mecparts/TeensyBoardZ80/src/cpu.h

#ifndef CPU_H
#define CPU_H

/* see main.c for definition */

int32 PCX; /* external view of PC                          */
int32 AF;  /* AF register                                  */
int32 BC;  /* BC register                                  */
int32 DE;  /* DE register                                  */
int32 HL;  /* HL register                                  */
int32 IX;  /* IX register                                  */
int32 IY;  /* IY register                                  */
int32 PC;  /* program counter                              */
int32 SP;  /* SP register                                  */
int32 AF1; /* alternate AF register                        */
int32 BC1; /* alternate BC register                        */
int32 DE1; /* alternate DE register                        */
int32 HL1; /* alternate HL register                        */
int32 IFF; /* Interrupt Flip Flop                          */
int32 IR;  /* Interrupt (upper) / Refresh (lower) register */
enum StatusType { 
	RUNNING,
	CBOOT,
	WBOOT,
	RETCCP 
} Status = RUNNING; /* Status of the CPU 0=running 1=end request 2=back to CCP */
int32 Debug = 0;
int32 Break = -1;
int32 Step = -1;

#ifdef iDEBUG
FILE* iLogFile;
char iLogBuffer[16];
const char* iLogTxt;
#endif

/*
	Functions needed by the soft CPU implementation
*/
void cpu_out(const uint32 Port, const uint32 Value) {
	_Bios();
}

uint32 cpu_in(const uint32 Port) {
	_Bdos();
	return(HIGH_REGISTER(AF));
}

/* Z80 Custom soft core */

/* simulator stop codes */
#define STOP_HALT       0   /* HALT                                             */
#define STOP_IBKPT      1   /* breakpoint   (program counter)                   */
#define STOP_MEM        2   /* breakpoint   (memory access)                     */
#define STOP_INSTR      3   /* breakpoint   (instruction access)                */
#define STOP_OPCODE     4   /* invalid operation encountered (8080, Z80, 8086)  */

#define ADDRMASK        0xffff

#define FLAG_C  1
#define FLAG_N  2
#define FLAG_P  4
#define FLAG_H  16
#define FLAG_Z  64
#define FLAG_S  128

#define SETFLAG(f,c)    (AF = (c) ? AF | FLAG_ ## f : AF & ~FLAG_ ## f)
#define TSTFLAG(f)      ((AF & FLAG_ ## f) != 0)

#define PARITY(x)   parityTable[(x) & 0xff]

#define SET_PVS(s)  (((cbits >> 6) ^ (cbits >> 5)) & 4)
#define SET_PV      (SET_PVS(sum))
#define SET_PV2(x)  ((temp == (x)) << 2)

#define POP(x)  {                               \
    register uint32 y = RAM_PP(SP);             \
    x = y + (RAM_PP(SP) << 8);                  \
}

#define JPC(cond) {                             \
    if (cond) {                                 \
        PC = GET_WORD(PC);                      \
    } else {                                    \
        PC += 2;                                \
    }                                           \
}

#define CALLC(cond) {                           \
    if (cond) {                                 \
        register uint32 adrr = GET_WORD(PC);    \
        PUSH(PC + 2);                           \
        PC = adrr;                              \
    } else {                                    \
        PC += 2;                                \
    }                                           \
}

/* the following tables precompute some common subexpressions
parityTable[i]          0..255  (number of 1's in i is odd) ? 0 : 4
incTable[i]             0..256! (i & 0xa8) | (((i & 0xff) == 0) << 6) | (((i & 0xf) == 0) << 4)
decTable[i]             0..255  (i & 0xa8) | (((i & 0xff) == 0) << 6) | (((i & 0xf) == 0xf) << 4) | 2
cbitsTable[i]           0..511  (i & 0x10) | ((i >> 8) & 1)
cbitsDup8Table[i]       0..511  (i & 0x10) | ((i >> 8) & 1) | ((i & 0xff) << 8) | (i & 0xa8) | (((i & 0xff) == 0) << 6)
cbitsDup16Table[i]      0..511  (i & 0x10) | ((i >> 8) & 1) | (i & 0x28)
cbits2Table[i]          0..511  (i & 0x10) | ((i >> 8) & 1) | 2
rrcaTable[i]            0..255  ((i & 1) << 15) | ((i >> 1) << 8) | ((i >> 1) & 0x28) | (i & 1)
rraTable[i]             0..255  ((i >> 1) << 8) | ((i >> 1) & 0x28) | (i & 1)
addTable[i]             0..511  ((i & 0xff) << 8) | (i & 0xa8) | (((i & 0xff) == 0) << 6)
subTable[i]             0..255  ((i & 0xff) << 8) | (i & 0xa8) | (((i & 0xff) == 0) << 6) | 2
andTable[i]             0..255  (i << 8) | (i & 0xa8) | ((i == 0) << 6) | 0x10 | parityTable[i]
xororTable[i]           0..255  (i << 8) | (i & 0xa8) | ((i == 0) << 6) | parityTable[i]
rotateShiftTable[i]     0..255  (i & 0xa8) | (((i & 0xff) == 0) << 6) | parityTable[i & 0xff]
incZ80Table[i]          0..256! (i & 0xa8) | (((i & 0xff) == 0) << 6) | (((i & 0xf) == 0) << 4) | ((i == 0x80) << 2)
decZ80Table[i]          0..255  (i & 0xa8) | (((i & 0xff) == 0) << 6) | (((i & 0xf) == 0xf) << 4) | ((i == 0x7f) << 2) | 2
cbitsZ80Table[i]        0..511  (i & 0x10) | (((i >> 6) ^ (i >> 5)) & 4) | ((i >> 8) & 1)
cbitsZ80DupTable[i]     0..511  (i & 0x10) | (((i >> 6) ^ (i >> 5)) & 4) | ((i >> 8) & 1) | (i & 0xa8)
cbits2Z80Table[i]       0..511  (i & 0x10) | (((i >> 6) ^ (i >> 5)) & 4) | ((i >> 8) & 1) | 2
cbits2Z80DupTable[i]    0..511  (i & 0x10) | (((i >> 6) ^ (i >> 5)) & 4) | ((i >> 8) & 1) | 2 | (i & 0xa8)
negTable[i]             0..255  (((i & 0x0f) != 0) << 4) | ((i == 0x80) << 2) | 2 | (i != 0)
rrdrldTable[i]          0..255  (i << 8) | (i & 0xa8) | (((i & 0xff) == 0) << 6) | parityTable[i]
cpTable[i]              0..255  (i & 0x80) | (((i & 0xff) == 0) << 6)
*/

/* parityTable[i] = (number of 1's in i is odd) ? 0 : 4, i = 0..255 */
static const uint8 parityTable[256] = {
	4,0,0,4,0,4,4,0,0,4,4,0,4,0,0,4,
	0,4,4,0,4,0,0,4,4,0,0,4,0,4,4,0,
	0,4,4,0,4,0,0,4,4,0,0,4,0,4,4,0,
	4,0,0,4,0,4,4,0,0,4,4,0,4,0,0,4,
	0,4,4,0,4,0,0,4,4,0,0,4,0,4,4,0,
	4,0,0,4,0,4,4,0,0,4,4,0,4,0,0,4,
	4,0,0,4,0,4,4,0,0,4,4,0,4,0,0,4,
	0,4,4,0,4,0,0,4,4,0,0,4,0,4,4,0,
	0,4,4,0,4,0,0,4,4,0,0,4,0,4,4,0,
	4,0,0,4,0,4,4,0,0,4,4,0,4,0,0,4,
	4,0,0,4,0,4,4,0,0,4,4,0,4,0,0,4,
	0,4,4,0,4,0,0,4,4,0,0,4,0,4,4,0,
	4,0,0,4,0,4,4,0,0,4,4,0,4,0,0,4,
	0,4,4,0,4,0,0,4,4,0,0,4,0,4,4,0,
	0,4,4,0,4,0,0,4,4,0,0,4,0,4,4,0,
	4,0,0,4,0,4,4,0,0,4,4,0,4,0,0,4,
};

/* incTable[i] = (i & 0xa8) | (((i & 0xff) == 0) << 6) | (((i & 0xf) == 0) << 4), i = 0..256 */
static const uint8 incTable[257] = {
	80,  0,  0,  0,  0,  0,  0,  0,  8,  8,  8,  8,  8,  8,  8,  8,
	16,  0,  0,  0,  0,  0,  0,  0,  8,  8,  8,  8,  8,  8,  8,  8,
	48, 32, 32, 32, 32, 32, 32, 32, 40, 40, 40, 40, 40, 40, 40, 40,
	48, 32, 32, 32, 32, 32, 32, 32, 40, 40, 40, 40, 40, 40, 40, 40,
	16,  0,  0,  0,  0,  0,  0,  0,  8,  8,  8,  8,  8,  8,  8,  8,
	16,  0,  0,  0,  0,  0,  0,  0,  8,  8,  8,  8,  8,  8,  8,  8,
	48, 32, 32, 32, 32, 32, 32, 32, 40, 40, 40, 40, 40, 40, 40, 40,
	48, 32, 32, 32, 32, 32, 32, 32, 40, 40, 40, 40, 40, 40, 40, 40,
	144,128,128,128,128,128,128,128,136,136,136,136,136,136,136,136,
	144,128,128,128,128,128,128,128,136,136,136,136,136,136,136,136,
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
	0xd88c,0xd988,0xda88,0xdb8c,0xdc88,0xdd8c,0xde8c,0xdf88,
	0xe0a0,0xe1a4,0xe2a4,0xe3a0,0xe4a4,0xe5a0,0xe6a0,0xe7a4,
	0xe8ac,0xe9a8,0xeaa8,0xebac,0xeca8,0xedac,0xeeac,0xefa8,
	0xf0a4,0xf1a0,0xf2a0,0xf3a4,0xf4a0,0xf5a4,0xf6a4,0xf7a0,
	0xf8a8,0xf9ac,0xfaac,0xfba8,0xfcac,0xfda8,0xfea8,0xffac,
};

/* cpTable[i] = (i & 0x80) | (((i & 0xff) == 0) << 6), i = 0..255 */
static const uint8 cpTable[256] = {
	64,  0,  0,  0,  0,  0,  0,  0,  0,  0,  0,  0,  0,  0,  0,  0,
	0,  0,  0,  0,  0,  0,  0,  0,  0,  0,  0,  0,  0,  0,  0,  0,
	0,  0,  0,  0,  0,  0,  0,  0,  0,  0,  0,  0,  0,  0,  0,  0,
	0,  0,  0,  0,  0,  0,  0,  0,  0,  0,  0,  0,  0,  0,  0,  0,
	0,  0,  0,  0,  0,  0,  0,  0,  0,  0,  0,  0,  0,  0,  0,  0,
	0,  0,  0,  0,  0,  0,  0,  0,  0,  0,  0,  0,  0,  0,  0,  0,
	0,  0,  0,  0,  0,  0,  0,  0,  0,  0,  0,  0,  0,  0,  0,  0,
	0,  0,  0,  0,  0,  0,  0,  0,  0,  0,  0,  0,  0,  0,  0,  0,
	128,128,128,128,128,128,128,128,128,128,128,128,128,128,128,128,
	128,128,128,128,128,128,128,128,128,128,128,128,128,128,128,128,
	128,128,128,128,128,128,128,128,128,128,128,128,128,128,128,128,
	128,128,128,128,128,128,128,128,128,128,128,128,128,128,128,128,
	128,128,128,128,128,128,128,128,128,128,128,128,128,128,128,128,
	128,128,128,128,128,128,128,128,128,128,128,128,128,128,128,128,
	128,128,128,128,128,128,128,128,128,128,128,128,128,128,128,128,
	128,128,128,128,128,128,128,128,128,128,128,128,128,128,128,128,
};

#if defined(DEBUG) || defined(iDEBUG)
static const char* Mnemonics[256] =
{
	"NOP", "LD BC,#h", "LD (BC),A", "INC BC", "INC B", "DEC B", "LD B,*h", "RLCA",
	"EX AF,AF'", "ADD HL,BC", "LD A,(BC)", "DEC BC", "INC C", "DEC C", "LD C,*h", "RRCA",
	"DJNZ @h", "LD DE,#h", "LD (DE),A", "INC DE", "INC D", "DEC D", "LD D,*h", "RLA",
	"JR @h", "ADD HL,DE", "LD A,(DE)", "DEC DE", "INC E", "DEC E", "LD E,*h", "RRA",
	"JR NZ,@h", "LD HL,#h", "LD (#h),HL", "INC HL", "INC H", "DEC H", "LD H,*h", "DAA",
	"JR Z,@h", "ADD HL,HL", "LD HL,(#h)", "DEC HL", "INC L", "DEC L", "LD L,*h", "CPL",
	"JR NC,@h", "LD SP,#h", "LD (#h),A", "INC SP", "INC (HL)", "DEC (HL)", "LD (HL),*h", "SCF",
	"JR C,@h", "ADD HL,SP", "LD A,(#h)", "DEC SP", "INC A", "DEC A", "LD A,*h", "CCF",
	"LD B,B", "LD B,C", "LD B,D", "LD B,E", "LD B,H", "LD B,L", "LD B,(HL)", "LD B,A",
	"LD C,B", "LD C,C", "LD C,D", "LD C,E", "LD C,H", "LD C,L", "LD C,(HL)", "LD C,A",
	"LD D,B", "LD D,C", "LD D,D", "LD D,E", "LD D,H", "LD D,L", "LD D,(HL)", "LD D,A",
	"LD E,B", "LD E,C", "LD E,D", "LD E,E", "LD E,H", "LD E,L", "LD E,(HL)", "LD E,A",
	"LD H,B", "LD H,C", "LD H,D", "LD H,E", "LD H,H", "LD H,L", "LD H,(HL)", "LD H,A",
	"LD L,B", "LD L,C", "LD L,D", "LD L,E", "LD L,H", "LD L,L", "LD L,(HL)", "LD L,A",
	"LD (HL),B", "LD (HL),C", "LD (HL),D", "LD (HL),E", "LD (HL),H", "LD (HL),L", "HALT", "LD (HL),A",
	"LD A,B", "LD A,C", "LD A,D", "LD A,E", "LD A,H", "LD A,L", "LD A,(HL)", "LD A,A",
	"ADD B", "ADD C", "ADD D", "ADD E", "ADD H", "ADD L", "ADD (HL)", "ADD A",
	"ADC B", "ADC C", "ADC D", "ADC E", "ADC H", "ADC L", "ADC (HL)", "ADC A",
	"SUB B", "SUB C", "SUB D", "SUB E", "SUB H", "SUB L", "SUB (HL)", "SUB A",
	"SBC B", "SBC C", "SBC D", "SBC E", "SBC H", "SBC L", "SBC (HL)", "SBC A",
	"AND B", "AND C", "AND D", "AND E", "AND H", "AND L", "AND (HL)", "AND A",
	"XOR B", "XOR C", "XOR D", "XOR E", "XOR H", "XOR L", "XOR (HL)", "XOR A",
	"OR B", "OR C", "OR D", "OR E", "OR H", "OR L", "OR (HL)", "OR A",
	"CP B", "CP C", "CP D", "CP E", "CP H", "CP L", "CP (HL)", "CP A",
	"RET NZ", "POP BC", "JP NZ,#h", "JP #h", "CALL NZ,#h", "PUSH BC", "ADD *h", "RST 00h",
	"RET Z", "RET", "JP Z,#h", "PFX_CB", "CALL Z,#h", "CALL #h", "ADC *h", "RST 08h",
	"RET NC", "POP DE", "JP NC,#h", "OUTA (*h)", "CALL NC,#h", "PUSH DE", "SUB *h", "RST 10h",
	"RET C", "EXX", "JP C,#h", "INA (*h)", "CALL C,#h", "PFX_DD", "SBC *h", "RST 18h",
	"RET PO", "POP HL", "JP PO,#h", "EX HL,(SP)", "CALL PO,#h", "PUSH HL", "AND *h", "RST 20h",
	"RET PE", "LD PC,HL", "JP PE,#h", "EX DE,HL", "CALL PE,#h", "PFX_ED", "XOR *h", "RST 28h",
	"RET P", "POP AF", "JP P,#h", "DI", "CALL P,#h", "PUSH AF", "OR *h", "RST 30h",
	"RET M", "LD SP,HL", "JP M,#h", "EI", "CALL M,#h", "PFX_FD", "CP *h", "RST 38h"
};

static const char* MnemonicsCB[256] =
{
	"RLC B", "RLC C", "RLC D", "RLC E", "RLC H", "RLC L", "RLC (HL)", "RLC A",
	"RRC B", "RRC C", "RRC D", "RRC E", "RRC H", "RRC L", "RRC (HL)", "RRC A",
	"RL B", "RL C", "RL D", "RL E", "RL H", "RL L", "RL (HL)", "RL A",
	"RR B", "RR C", "RR D", "RR E", "RR H", "RR L", "RR (HL)", "RR A",
	"SLA B", "SLA C", "SLA D", "SLA E", "SLA H", "SLA L", "SLA (HL)", "SLA A",
	"SRA B", "SRA C", "SRA D", "SRA E", "SRA H", "SRA L", "SRA (HL)", "SRA A",
	"SLL B", "SLL C", "SLL D", "SLL E", "SLL H", "SLL L", "SLL (HL)", "SLL A",
	"SRL B", "SRL C", "SRL D", "SRL E", "SRL H", "SRL L", "SRL (HL)", "SRL A",
	"BIT 0,B", "BIT 0,C", "BIT 0,D", "BIT 0,E", "BIT 0,H", "BIT 0,L", "BIT 0,(HL)", "BIT 0,A",
	"BIT 1,B", "BIT 1,C", "BIT 1,D", "BIT 1,E", "BIT 1,H", "BIT 1,L", "BIT 1,(HL)", "BIT 1,A",
	"BIT 2,B", "BIT 2,C", "BIT 2,D", "BIT 2,E", "BIT 2,H", "BIT 2,L", "BIT 2,(HL)", "BIT 2,A",
	"BIT 3,B", "BIT 3,C", "BIT 3,D", "BIT 3,E", "BIT 3,H", "BIT 3,L", "BIT 3,(HL)", "BIT 3,A",
	"BIT 4,B", "BIT 4,C", "BIT 4,D", "BIT 4,E", "BIT 4,H", "BIT 4,L", "BIT 4,(HL)", "BIT 4,A",
	"BIT 5,B", "BIT 5,C", "BIT 5,D", "BIT 5,E", "BIT 5,H", "BIT 5,L", "BIT 5,(HL)", "BIT 5,A",
	"BIT 6,B", "BIT 6,C", "BIT 6,D", "BIT 6,E", "BIT 6,H", "BIT 6,L", "BIT 6,(HL)", "BIT 6,A",
	"BIT 7,B", "BIT 7,C", "BIT 7,D", "BIT 7,E", "BIT 7,H", "BIT 7,L", "BIT 7,(HL)", "BIT 7,A",
	"RES 0,B", "RES 0,C", "RES 0,D", "RES 0,E", "RES 0,H", "RES 0,L", "RES 0,(HL)", "RES 0,A",
	"RES 1,B", "RES 1,C", "RES 1,D", "RES 1,E", "RES 1,H", "RES 1,L", "RES 1,(HL)", "RES 1,A",
	"RES 2,B", "RES 2,C", "RES 2,D", "RES 2,E", "RES 2,H", "RES 2,L", "RES 2,(HL)", "RES 2,A",
	"RES 3,B", "RES 3,C", "RES 3,D", "RES 3,E", "RES 3,H", "RES 3,L", "RES 3,(HL)", "RES 3,A",
	"RES 4,B", "RES 4,C", "RES 4,D", "RES 4,E", "RES 4,H", "RES 4,L", "RES 4,(HL)", "RES 4,A",
	"RES 5,B", "RES 5,C", "RES 5,D", "RES 5,E", "RES 5,H", "RES 5,L", "RES 5,(HL)", "RES 5,A",
	"RES 6,B", "RES 6,C", "RES 6,D", "RES 6,E", "RES 6,H", "RES 6,L", "RES 6,(HL)", "RES 6,A",
	"RES 7,B", "RES 7,C", "RES 7,D", "RES 7,E", "RES 7,H", "RES 7,L", "RES 7,(HL)", "RES 7,A",
	"SET 0,B", "SET 0,C", "SET 0,D", "SET 0,E", "SET 0,H", "SET 0,L", "SET 0,(HL)", "SET 0,A",
	"SET 1,B", "SET 1,C", "SET 1,D", "SET 1,E", "SET 1,H", "SET 1,L", "SET 1,(HL)", "SET 1,A",
	"SET 2,B", "SET 2,C", "SET 2,D", "SET 2,E", "SET 2,H", "SET 2,L", "SET 2,(HL)", "SET 2,A",
	"SET 3,B", "SET 3,C", "SET 3,D", "SET 3,E", "SET 3,H", "SET 3,L", "SET 3,(HL)", "SET 3,A",
	"SET 4,B", "SET 4,C", "SET 4,D", "SET 4,E", "SET 4,H", "SET 4,L", "SET 4,(HL)", "SET 4,A",
	"SET 5,B", "SET 5,C", "SET 5,D", "SET 5,E", "SET 5,H", "SET 5,L", "SET 5,(HL)", "SET 5,A",
	"SET 6,B", "SET 6,C", "SET 6,D", "SET 6,E", "SET 6,H", "SET 6,L", "SET 6,(HL)", "SET 6,A",
	"SET 7,B", "SET 7,C", "SET 7,D", "SET 7,E", "SET 7,H", "SET 7,L", "SET 7,(HL)", "SET 7,A"
};

static const char* MnemonicsED[256] =
{
	"DB EDh,00h", "DB EDh,01h", "DB EDh,02h", "DB EDh,03h",
	"DB EDh,04h", "DB EDh,05h", "DB EDh,06h", "DB EDh,07h",
	"DB EDh,08h", "DB EDh,09h", "DB EDh,0Ah", "DB EDh,0Bh",
	"DB EDh,0Ch", "DB EDh,0Dh", "DB EDh,0Eh", "DB EDh,0Fh",
	"DB EDh,10h", "DB EDh,11h", "DB EDh,12h", "DB EDh,13h",
	"DB EDh,14h", "DB EDh,15h", "DB EDh,16h", "DB EDh,17h",
	"DB EDh,18h", "DB EDh,19h", "DB EDh,1Ah", "DB EDh,1Bh",
	"DB EDh,1Ch", "DB EDh,1Dh", "DB EDh,1Eh", "DB EDh,1Fh",
	"DB EDh,20h", "DB EDh,21h", "DB EDh,22h", "DB EDh,23h",
	"DB EDh,24h", "DB EDh,25h", "DB EDh,26h", "DB EDh,27h",
	"DB EDh,28h", "DB EDh,29h", "DB EDh,2Ah", "DB EDh,2Bh",
	"DB EDh,2Ch", "DB EDh,2Dh", "DB EDh,2Eh", "DB EDh,2Fh",
	"DB EDh,30h", "DB EDh,31h", "DB EDh,32h", "DB EDh,33h",
	"DB EDh,34h", "DB EDh,35h", "DB EDh,36h", "DB EDh,37h",
	"DB EDh,38h", "DB EDh,39h", "DB EDh,3Ah", "DB EDh,3Bh",
	"DB EDh,3Ch", "DB EDh,3Dh", "DB EDh,3Eh", "DB EDh,3Fh",
	"IN B,(C)", "OUT (C),B", "SBC HL,BC", "LD (#h),BC",
	"NEG", "RETN", "IM 0", "LD I,A",
	"IN C,(C)", "OUT (C),C", "ADC HL,BC", "LD BC,(#h)",
	"DB EDh,4Ch", "RETI", "DB EDh,4Eh", "LD R,A",
	"IN D,(C)", "OUT (C),D", "SBC HL,DE", "LD (#h),DE",
	"DB EDh,54h", "DB EDh,55h", "IM 1", "LD A,I",
	"IN E,(C)", "OUT (C),E", "ADC HL,DE", "LD DE,(#h)",
	"DB EDh,5Ch", "DB EDh,5Dh", "IM 2", "LD A,R",
	"IN H,(C)", "OUT (C),H", "SBC HL,HL", "LD (#h),HL",
	"DB EDh,64h", "DB EDh,65h", "DB EDh,66h", "RRD",
	"IN L,(C)", "OUT (C),L", "ADC HL,HL", "LD HL,(#h)",
	"DB EDh,6Ch", "DB EDh,6Dh", "DB EDh,6Eh", "RLD",
	"IN F,(C)", "DB EDh,71h", "SBC HL,SP", "LD (#h),SP",
	"DB EDh,74h", "DB EDh,75h", "DB EDh,76h", "DB EDh,77h",
	"IN A,(C)", "OUT (C),A", "ADC HL,SP", "LD SP,(#h)",
	"DB EDh,7Ch", "DB EDh,7Dh", "DB EDh,7Eh", "DB EDh,7Fh",
	"DB EDh,80h", "DB EDh,81h", "DB EDh,82h", "DB EDh,83h",
	"DB EDh,84h", "DB EDh,85h", "DB EDh,86h", "DB EDh,87h",
	"DB EDh,88h", "DB EDh,89h", "DB EDh,8Ah", "DB EDh,8Bh",
	"DB EDh,8Ch", "DB EDh,8Dh", "DB EDh,8Eh", "DB EDh,8Fh",
	"DB EDh,90h", "DB EDh,91h", "DB EDh,92h", "DB EDh,93h",
	"DB EDh,94h", "DB EDh,95h", "DB EDh,96h", "DB EDh,97h",
	"DB EDh,98h", "DB EDh,99h", "DB EDh,9Ah", "DB EDh,9Bh",
	"DB EDh,9Ch", "DB EDh,9Dh", "DB EDh,9Eh", "DB EDh,9Fh",
	"LDI", "CPI", "INI", "OUTI",
	"DB EDh,A4h", "DB EDh,A5h", "DB EDh,A6h", "DB EDh,A7h",
	"LDD", "CPD", "IND", "OUTD",
	"DB EDh,ACh", "DB EDh,ADh", "DB EDh,AEh", "DB EDh,AFh",
	"LDIR", "CPIR", "INIR", "OTIR",
	"DB EDh,B4h", "DB EDh,B5h", "DB EDh,B6h", "DB EDh,B7h",
	"LDDR", "CPDR", "INDR", "OTDR",
	"DB EDh,BCh", "DB EDh,BDh", "DB EDh,BEh", "DB EDh,BFh",
	"DB EDh,C0h", "DB EDh,C1h", "DB EDh,C2h", "DB EDh,C3h",
	"DB EDh,C4h", "DB EDh,C5h", "DB EDh,C6h", "DB EDh,C7h",
	"DB EDh,C8h", "DB EDh,C9h", "DB EDh,CAh", "DB EDh,CBh",
	"DB EDh,CCh", "DB EDh,CDh", "DB EDh,CEh", "DB EDh,CFh",
	"DB EDh,D0h", "DB EDh,D1h", "DB EDh,D2h", "DB EDh,D3h",
	"DB EDh,D4h", "DB EDh,D5h", "DB EDh,D6h", "DB EDh,D7h",
	"DB EDh,D8h", "DB EDh,D9h", "DB EDh,DAh", "DB EDh,DBh",
	"DB EDh,DCh", "DB EDh,DDh", "DB EDh,DEh", "DB EDh,DFh",
	"DB EDh,E0h", "DB EDh,E1h", "DB EDh,E2h", "DB EDh,E3h",
	"DB EDh,E4h", "DB EDh,E5h", "DB EDh,E6h", "DB EDh,E7h",
	"DB EDh,E8h", "DB EDh,E9h", "DB EDh,EAh", "DB EDh,EBh",
	"DB EDh,ECh", "DB EDh,EDh", "DB EDh,EEh", "DB EDh,EFh",
	"DB EDh,F0h", "DB EDh,F1h", "DB EDh,F2h", "DB EDh,F3h",
	"DB EDh,F4h", "DB EDh,F5h", "DB EDh,F6h", "DB EDh,F7h",
	"DB EDh,F8h", "DB EDh,F9h", "DB EDh,FAh", "DB EDh,FBh",
	"DB EDh,FCh", "DB EDh,FDh", "DB EDh,FEh", "DB EDh,FFh"
};

static const char* MnemonicsXX[256] =
{
	"NOP", "LD BC,#h", "LD (BC),A", "INC BC", "INC B", "DEC B", "LD B,*h", "RLCA",
	"EX AF,AF'", "ADD I%,BC", "LD A,(BC)", "DEC BC", "INC C", "DEC C", "LD C,*h", "RRCA",
	"DJNZ @h", "LD DE,#h", "LD (DE),A", "INC DE", "INC D", "DEC D", "LD D,*h", "RLA",
	"JR @h", "ADD I%,DE", "LD A,(DE)", "DEC DE", "INC E", "DEC E", "LD E,*h", "RRA",
	"JR NZ,@h", "LD I%,#h", "LD (#h),I%", "INC I%", "INC I%h", "DEC I%h", "LD I%h,*h", "DAA",
	"JR Z,@h", "ADD I%,I%", "LD I%,(#h)", "DEC I%", "INC I%l", "DEC I%l", "LD I%l,*h", "CPL",
	"JR NC,@h", "LD SP,#h", "LD (#h),A", "INC SP", "INC (I%+^h)", "DEC (I%+^h)", "LD (I%+^h),*h", "SCF",
	"JR C,@h", "ADD I%,SP", "LD A,(#h)", "DEC SP", "INC A", "DEC A", "LD A,*h", "CCF",
	"LD B,B", "LD B,C", "LD B,D", "LD B,E", "LD B,I%h", "LD B,I%l", "LD B,(I%+^h)", "LD B,A",
	"LD C,B", "LD C,C", "LD C,D", "LD C,E", "LD C,I%h", "LD C,I%l", "LD C,(I%+^h)", "LD C,A",
	"LD D,B", "LD D,C", "LD D,D", "LD D,E", "LD D,I%h", "LD D,I%l", "LD D,(I%+^h)", "LD D,A",
	"LD E,B", "LD E,C", "LD E,D", "LD E,E", "LD E,I%h", "LD E,I%l", "LD E,(I%+^h)", "LD E,A",
	"LD I%h,B", "LD I%h,C", "LD I%h,D", "LD I%h,E", "LD I%h,I%h", "LD I%h,I%l", "LD H,(I%+^h)", "LD I%h,A",
	"LD I%l,B", "LD I%l,C", "LD I%l,D", "LD I%l,E", "LD I%l,I%h", "LD I%l,I%l", "LD L,(I%+^h)", "LD I%l,A",
	"LD (I%+^h),B", "LD (I%+^h),C", "LD (I%+^h),D", "LD (I%+^h),E", "LD (I%+^h),H", "LD (I%+^h),L", "HALT", "LD (I%+^h),A",
	"LD A,B", "LD A,C", "LD A,D", "LD A,E", "LD A,I%h", "LD A,I%l", "LD A,(I%+^h)", "LD A,A",
	"ADD B", "ADD C", "ADD D", "ADD E", "ADD I%h", "ADD I%l", "ADD (I%+^h)", "ADD A",
	"ADC B", "ADC C", "ADC D", "ADC E", "ADC I%h", "ADC I%l", "ADC (I%+^h)", "ADC,A",
	"SUB B", "SUB C", "SUB D", "SUB E", "SUB I%h", "SUB I%l", "SUB (I%+^h)", "SUB A",
	"SBC B", "SBC C", "SBC D", "SBC E", "SBC I%h", "SBC I%l", "SBC (I%+^h)", "SBC A",
	"AND B", "AND C", "AND D", "AND E", "AND I%h", "AND I%l", "AND (I%+^h)", "AND A",
	"XOR B", "XOR C", "XOR D", "XOR E", "XOR I%h", "XOR I%l", "XOR (I%+^h)", "XOR A",
	"OR B", "OR C", "OR D", "OR E", "OR I%h", "OR I%l", "OR (I%+^h)", "OR A",
	"CP B", "CP C", "CP D", "CP E", "CP I%h", "CP I%l", "CP (I%+^h)", "CP A",
	"RET NZ", "POP BC", "JP NZ,#h", "JP #h", "CALL NZ,#h", "PUSH BC", "ADD *h", "RST 00h",
	"RET Z", "RET", "JP Z,#h", "PFX_CB", "CALL Z,#h", "CALL #h", "ADC *h", "RST 08h",
	"RET NC", "POP DE", "JP NC,#h", "OUTA (*h)", "CALL NC,#h", "PUSH DE", "SUB *h", "RST 10h",
	"RET C", "EXX", "JP C,#h", "INA (*h)", "CALL C,#h", "PFX_DD", "SBC *h", "RST 18h",
	"RET PO", "POP I%", "JP PO,#h", "EX I%,(SP)", "CALL PO,#h", "PUSH I%", "AND *h", "RST 20h",
	"RET PE", "LD PC,I%", "JP PE,#h", "EX DE,I%", "CALL PE,#h", "PFX_ED", "XOR *h", "RST 28h",
	"RET P", "POP AF", "JP P,#h", "DI", "CALL P,#h", "PUSH AF", "OR *h", "RST 30h",
	"RET M", "LD SP,I%", "JP M,#h", "EI", "CALL M,#h", "PFX_FD", "CP *h", "RST 38h"
};

static const char* MnemonicsXCB[256] =
{
	"RLC B", "RLC C", "RLC D", "RLC E", "RLC H", "RLC L", "RLC (I%@h)", "RLC A",
	"RRC B", "RRC C", "RRC D", "RRC E", "RRC H", "RRC L", "RRC (I%@h)", "RRC A",
	"RL B", "RL C", "RL D", "RL E", "RL H", "RL L", "RL (I%@h)", "RL A",
	"RR B", "RR C", "RR D", "RR E", "RR H", "RR L", "RR (I%@h)", "RR A",
	"SLA B", "SLA C", "SLA D", "SLA E", "SLA H", "SLA L", "SLA (I%@h)", "SLA A",
	"SRA B", "SRA C", "SRA D", "SRA E", "SRA H", "SRA L", "SRA (I%@h)", "SRA A",
	"SLL B", "SLL C", "SLL D", "SLL E", "SLL H", "SLL L", "SLL (I%@h)", "SLL A",
	"SRL B", "SRL C", "SRL D", "SRL E", "SRL H", "SRL L", "SRL (I%@h)", "SRL A",
	"BIT 0,B", "BIT 0,C", "BIT 0,D", "BIT 0,E", "BIT 0,H", "BIT 0,L", "BIT 0,(I%@h)", "BIT 0,A",
	"BIT 1,B", "BIT 1,C", "BIT 1,D", "BIT 1,E", "BIT 1,H", "BIT 1,L", "BIT 1,(I%@h)", "BIT 1,A",
	"BIT 2,B", "BIT 2,C", "BIT 2,D", "BIT 2,E", "BIT 2,H", "BIT 2,L", "BIT 2,(I%@h)", "BIT 2,A",
	"BIT 3,B", "BIT 3,C", "BIT 3,D", "BIT 3,E", "BIT 3,H", "BIT 3,L", "BIT 3,(I%@h)", "BIT 3,A",
	"BIT 4,B", "BIT 4,C", "BIT 4,D", "BIT 4,E", "BIT 4,H", "BIT 4,L", "BIT 4,(I%@h)", "BIT 4,A",
	"BIT 5,B", "BIT 5,C", "BIT 5,D", "BIT 5,E", "BIT 5,H", "BIT 5,L", "BIT 5,(I%@h)", "BIT 5,A",
	"BIT 6,B", "BIT 6,C", "BIT 6,D", "BIT 6,E", "BIT 6,H", "BIT 6,L", "BIT 6,(I%@h)", "BIT 6,A",
	"BIT 7,B", "BIT 7,C", "BIT 7,D", "BIT 7,E", "BIT 7,H", "BIT 7,L", "BIT 7,(I%@h)", "BIT 7,A",
	"RES 0,B", "RES 0,C", "RES 0,D", "RES 0,E", "RES 0,H", "RES 0,L", "RES 0,(I%@h)", "RES 0,A",
	"RES 1,B", "RES 1,C", "RES 1,D", "RES 1,E", "RES 1,H", "RES 1,L", "RES 1,(I%@h)", "RES 1,A",
	"RES 2,B", "RES 2,C", "RES 2,D", "RES 2,E", "RES 2,H", "RES 2,L", "RES 2,(I%@h)", "RES 2,A",
	"RES 3,B", "RES 3,C", "RES 3,D", "RES 3,E", "RES 3,H", "RES 3,L", "RES 3,(I%@h)", "RES 3,A",
	"RES 4,B", "RES 4,C", "RES 4,D", "RES 4,E", "RES 4,H", "RES 4,L", "RES 4,(I%@h)", "RES 4,A",
	"RES 5,B", "RES 5,C", "RES 5,D", "RES 5,E", "RES 5,H", "RES 5,L", "RES 5,(I%@h)", "RES 5,A",
	"RES 6,B", "RES 6,C", "RES 6,D", "RES 6,E", "RES 6,H", "RES 6,L", "RES 6,(I%@h)", "RES 6,A",
	"RES 7,B", "RES 7,C", "RES 7,D", "RES 7,E", "RES 7,H", "RES 7,L", "RES 7,(I%@h)", "RES 7,A",
	"SET 0,B", "SET 0,C", "SET 0,D", "SET 0,E", "SET 0,H", "SET 0,L", "SET 0,(I%@h)", "SET 0,A",
	"SET 1,B", "SET 1,C", "SET 1,D", "SET 1,E", "SET 1,H", "SET 1,L", "SET 1,(I%@h)", "SET 1,A",
	"SET 2,B", "SET 2,C", "SET 2,D", "SET 2,E", "SET 2,H", "SET 2,L", "SET 2,(I%@h)", "SET 2,A",
	"SET 3,B", "SET 3,C", "SET 3,D", "SET 3,E", "SET 3,H", "SET 3,L", "SET 3,(I%@h)", "SET 3,A",
	"SET 4,B", "SET 4,C", "SET 4,D", "SET 4,E", "SET 4,H", "SET 4,L", "SET 4,(I%@h)", "SET 4,A",
	"SET 5,B", "SET 5,C", "SET 5,D", "SET 5,E", "SET 5,H", "SET 5,L", "SET 5,(I%@h)", "SET 5,A",
	"SET 6,B", "SET 6,C", "SET 6,D", "SET 6,E", "SET 6,H", "SET 6,L", "SET 6,(I%@h)", "SET 6,A",
	"SET 7,B", "SET 7,C", "SET 7,D", "SET 7,E", "SET 7,H", "SET 7,L", "SET 7,(I%@h)", "SET 7,A"
};

static const char* CPMCalls[41] =
{
	"System Reset", "Console Input", "Console Output", "Reader Input", "Punch Output", "List Output", "Direct I/O", "Get IOByte",
	"Set IOByte", "Print String", "Read Buffered", "Console Status", "Get Version", "Reset Disk", "Select Disk", "Open File",
	"Close File", "Search First", "Search Next", "Delete File", "Read Sequential", "Write Sequential", "Make File", "Rename File",
	"Get Login Vector", "Get Current Disk", "Set DMA Address", "Get Alloc", "Write Protect Disk", "Get R/O Vector", "Set File Attr", "Get Disk Params",
	"Get/Set User", "Read Random", "Write Random", "Get File Size", "Set Random Record", "Reset Drive", "N/A", "N/A", "Write Random 0 fill"
};

int32 Watch = -1;
#endif

/* Memory management    */
static uint8 GET_BYTE(register uint32 Addr) {
	return _RamRead(Addr & ADDRMASK);
}

static void PUT_BYTE(register uint32 Addr, register uint32 Value) {
	_RamWrite(Addr & ADDRMASK, Value);
}

static uint16 GET_WORD(register uint32 a) {
	return GET_BYTE(a) | (GET_BYTE(a + 1) << 8);
}

static void PUT_WORD(register uint32 Addr, register uint32 Value) {
	_RamWrite(Addr, Value);
	_RamWrite(++Addr, Value >> 8);
}

#define RAM_MM(a)   GET_BYTE(a--)
#define RAM_PP(a)   GET_BYTE(a++)

#define PUT_BYTE_PP(a,v) PUT_BYTE(a++, v)
#define PUT_BYTE_MM(a,v) PUT_BYTE(a--, v)
#define MM_PUT_BYTE(a,v) PUT_BYTE(--a, v)

#define PUSH(x) do {            \
	MM_PUT_BYTE(SP, (x) >> 8);  \
	MM_PUT_BYTE(SP, x);         \
} while (0)

/*  Macros for the IN/OUT instructions INI/INIR/IND/INDR/OUTI/OTIR/OUTD/OTDR

Pre condition
temp == value of register B at entry of the instruction
acu == value of transferred byte (IN or OUT)
Post condition
F is set correctly

Use INOUTFLAGS_ZERO(x) for INIR/INDR/OTIR/OTDR where
x == (C + 1) & 0xff for INIR
x == L              for OTIR and OTDR
x == (C - 1) & 0xff for INDR
Use INOUTFLAGS_NONZERO(x) for INI/IND/OUTI/OUTD where
x == (C + 1) & 0xff for INI
x == L              for OUTI and OUTD
x == (C - 1) & 0xff for IND
*/
#define INOUTFLAGS(syxz, x)                                             \
    AF = (AF & 0xff00) | (syxz) |               /* SF, YF, XF, ZF   */  \
        ((acu & 0x80) >> 6) |                           /* NF       */  \
        ((acu + (x)) > 0xff ? (FLAG_C | FLAG_H) : 0) |  /* CF, HF   */  \
        parityTable[((acu + (x)) & 7) ^ temp]           /* PF       */

#define INOUTFLAGS_ZERO(x)      INOUTFLAGS(FLAG_Z, x)
#define INOUTFLAGS_NONZERO(x)                                           \
    INOUTFLAGS((HIGH_REGISTER(BC) & 0xa8) | ((HIGH_REGISTER(BC) == 0) << 6), x)

static inline void Z80reset(void) {
	PC = 0;
	IFF = 0;
	IR = 0;
	Status = RUNNING;
	Debug = 0;
	Break = -1;
	Step = -1;
}

#ifdef DEBUG
void watchprint(uint16 pos) {
	uint8 I, J;
	_puts("\r\n");
	_puts("  Watch : "); _puthex16(Watch);
	_puts(" = "); _puthex8(_RamRead(Watch)); _putcon(':'); _puthex8(_RamRead(Watch + 1));
	_puts(" / ");
	for (J = 0, I = _RamRead(Watch); J < 8; ++J, I <<= 1) _putcon(I & 0x80 ? '1' : '0');
	_putcon(':');
	for (J = 0, I = _RamRead(Watch + 1); J < 8; ++J, I <<= 1) _putcon(I & 0x80 ? '1' : '0');
}

void memdump(uint16 pos) {
	uint16 h = pos;
	uint16 c = pos;
	uint8 l, i;
	uint8 ch = pos & 0xff;

	_puts("       ");
	for (i = 0; i < 16; ++i) {
		_puthex8(ch++ & 0x0f);
		_puts(" ");
	}
	_puts("\r\n");
	_puts("       ");
	for (i = 0; i < 16; ++i)
		_puts("---");
	_puts("\r\n");
	for (l = 0; l < 16; ++l) {
		_puthex16(h);
		_puts(" : ");
		for (i = 0; i < 16; ++i) {
			_puthex8(_RamRead(h++));
			_puts(" ");
		}
		for (i = 0; i < 16; ++i) {
			ch = _RamRead(c++);
			_putcon(ch > 31 && ch < 127 ? ch : '.');
		}
		_puts("\r\n");
	}
}

uint8 Disasm(uint16 pos) {
	const char* txt;
	char jr;
	uint8 ch = _RamRead(pos);
	uint8 count = 1;
	uint8 C = '?';

	switch (ch) {
	case 0xCB: ++pos; txt = MnemonicsCB[_RamRead(pos++)]; count++; break;
	case 0xED: ++pos; txt = MnemonicsED[_RamRead(pos++)]; count++; break;
	case 0xDD: ++pos; C = 'X';
		if (_RamRead(pos) != 0xCB) {
			txt = MnemonicsXX[_RamRead(pos++)]; ++count;
		} else {
			++pos; txt = MnemonicsXCB[_RamRead(pos++)]; count += 2;
		}
		break;
	case 0xFD: ++pos; C = 'Y';
		if (_RamRead(pos) != 0xCB) {
			txt = MnemonicsXX[_RamRead(pos++)]; ++count;
		} else {
			++pos; txt = MnemonicsXCB[_RamRead(pos++)]; count += 2;
		}
		break;
	default:   txt = Mnemonics[_RamRead(pos++)];
	}
	while (*txt != 0) {
		switch (*txt) {
		case '*':
			txt += 2;
			++count;
			_puthex8(_RamRead(pos++));
			break;
		case '^':
			txt += 2;
			++count;
			_puthex8(_RamRead(pos++));
			break;
		case '#':
			txt += 2;
			count += 2;
			_puthex8(_RamRead(pos + 1));
			_puthex8(_RamRead(pos));
			break;
		case '@':
			txt += 2;
			++count;
			jr = _RamRead(pos++);
			_puthex16(pos + jr);
			break;
		case '%':
			_putch(C);
			++txt;
			break;
		default:
			_putch(*txt);
			++txt;
		}
	}

	return(count);
}

void Z80debug(void) {
	uint8 ch = 0;
	uint16 pos, l;
	static const char Flags[9] = "SZ5H3PNC";
	uint8 J, I;
	unsigned int bpoint;
	uint8 loop = TRUE;

	while (loop) {
		pos = PC;
		_puts("\r\n");
		_puts("BC:");  _puthex16(BC);
		_puts(" DE:"); _puthex16(DE);
		_puts(" HL:"); _puthex16(HL);
		_puts(" AF:"); _puthex16(AF);
		_puts(" : [");
		for (J = 0, I = LOW_REGISTER(AF); J < 8; ++J, I <<= 1) _putcon(I & 0x80 ? Flags[J] : '.');
		_puts("]\r\n");
		_puts("IX:");  _puthex16(IX);
		_puts(" IY:"); _puthex16(IY);
		_puts(" SP:"); _puthex16(SP);
		_puts(" PC:"); _puthex16(PC);
		_puts(" : ");

		Disasm(pos);

		if (PC == 0x0005) {
			if (LOW_REGISTER(BC) > 40) {
				_puts(" (Unknown)");
			} else {
				_puts(" (");
				_puts(CPMCalls[LOW_REGISTER(BC)]);
				_puts(")");
			}
		}

		if (Watch != -1) {
			watchprint(Watch);
		}

		_puts("\r\n");
		_puts("Command|? : ");
		ch = _getch();
		if (ch > 21 && ch < 127)
			_putch(ch);
		switch (ch) {
		case 't':
			loop = FALSE;
			break;
		case 'c':
			loop = FALSE;
			_puts("\r\n");
			Debug = 0;
			break;
		case 'b':
			_puts("\r\n"); memdump(BC); break;
		case 'd':
			_puts("\r\n"); memdump(DE); break;
		case 'h':
			_puts("\r\n"); memdump(HL); break;
		case 'p':
			_puts("\r\n"); memdump(PC & 0xFF00); break;
		case 's':
			_puts("\r\n"); memdump(SP & 0xFF00); break;
		case 'x':
			_puts("\r\n"); memdump(IX & 0xFF00); break;
		case 'y':
			_puts("\r\n"); memdump(IY & 0xFF00); break;
		case 'a':
			_puts("\r\n"); memdump(dmaAddr); break;
		case 'l':
			_puts("\r\n");
			I = 16;
			l = pos;
			while (I > 0) {
				_puthex16(l);
				_puts(" : ");
				l += Disasm(l);
				_puts("\r\n");
				--I;
			}
			break;
		case 'B':
			_puts(" Addr: ");
			scanf("%04x", &bpoint);
			Break = bpoint;
			_puts("Breakpoint set to ");
			_puthex16(Break);
			_puts("\r\n");
			break;
		case 'C':
			Break = -1;
			_puts(" Breakpoint cleared\r\n");
			break;
		case 'D':
			_puts(" Addr: ");
			scanf("%04x", &bpoint);
			memdump(bpoint);
			break;
		case 'L':
			_puts(" Addr: ");
			scanf("%04x", &bpoint);
			I = 16;
			l = bpoint;
			while (I > 0) {
				_puthex16(l);
				_puts(" : ");
				l += Disasm(l);
				_puts("\r\n");
				--I;
			}
			break;
		case 'T':
			loop = FALSE;
			Step = pos + 3; // This only works correctly with CALL
							// If the called function messes with the stack, this will fail as well.
			Debug = 0;
			break;
		case 'W':
			_puts(" Addr: ");
			scanf("%04x", &bpoint);
			Watch = bpoint;
			_puts("Watch set to ");
			_puthex16(Watch);
			_puts("\r\n");
			break;
		case '?':
			_puts("\r\n");
			_puts("Lowercase commands:\r\n");
			_puts("  t - traces to the next instruction\r\n");
			_puts("  c - Continue execution\r\n");
			_puts("  b - Dumps memory pointed by (BC)\r\n");
			_puts("  d - Dumps memory pointed by (DE)\r\n");
			_puts("  h - Dumps memory pointed by (HL)\r\n");
			_puts("  p - Dumps the page (PC) points to\r\n");
			_puts("  s - Dumps the page (SP) points to\r\n");
			_puts("  x - Dumps the page (IX) points to\r\n");
			_puts("  y - Dumps the page (IY) points to\r\n");
			_puts("  a - Dumps memory pointed by dmaAddr\r\n");
			_puts("  l - Disassembles from current PC\r\n");
			_puts("Uppercase commands:\r\n");
			_puts("  B - Sets breakpoint at address\r\n");
			_puts("  C - Clears breakpoint\r\n");
			_puts("  D - Dumps memory at address\r\n");
			_puts("  L - Disassembles at address\r\n");
			_puts("  T - Steps over a call\r\n");
			_puts("  W - Sets a byte/word watch\r\n");
			break;
		default:
			_puts(" ???\r\n");
		}
	}
}
#endif

static inline void Z80run(void) {
	register uint32 temp = 0;
	register uint32 acu;
	register uint32 sum;
	register uint32 cbits;
	register uint32 op;
	register uint32 adr;

	/* main instruction fetch/decode loop */
	while (Status == RUNNING) {	/* loop until Status != 0 */

#ifdef DEBUG
		if (PC == Break) {
			_puts(":BREAK at ");
			_puthex16(Break);
			_puts(":");
			Debug = 1;
		}
		if (PC == Step) {
			Debug = 1;
			Step = -1;
		}
		if (Debug)
			Z80debug();
#endif

		PCX = PC;

#ifdef iDEBUG
		iLogFile = fopen("iDump.log", "a");
		switch (RAM[PCX & 0xffff]) {
		case 0xCB: iLogTxt = MnemonicsCB[RAM[PCX & 0xffff + 1]]; break;
		case 0xED: iLogTxt = MnemonicsED[RAM[PCX & 0xffff + 1]]; break;
		case 0xDD:
		case 0xFD:
			if (RAM[PCX & 0xffff] == 0xCB) {
				iLogTxt = MnemonicsXCB[RAM[PCX & 0xffff + 1]]; break;
			} else {
				iLogTxt = MnemonicsXX[RAM[PCX & 0xffff + 1]]; break;
			}
		default: iLogTxt = Mnemonics[RAM[PCX & 0xffff]];
		}
		sprintf(iLogBuffer, "0x%04x : 0x%02x = %s\n", PCX, RAM[PCX & 0xffff], iLogTxt);
		fputs(iLogBuffer, iLogFile);
		fclose(iLogFile);
#endif
		IR = (IR & 0xFF80) | ((IR + 1) & 0x7F);
		
		switch (RAM_PP(PC)) {

		case 0x00:      /* NOP */
			break;

		case 0x01:      /* LD BC,nnnn */
			BC = GET_WORD(PC);
			PC += 2;
			break;

		case 0x02:      /* LD (BC),A */
			PUT_BYTE(BC, HIGH_REGISTER(AF));
			break;

		case 0x03:      /* INC BC */
			++BC;
			break;

		case 0x04:      /* INC B */
			BC += 0x100;
			temp = HIGH_REGISTER(BC);
			AF = (AF & ~0xfe) | incTable[temp] | SET_PV2(0x80); /* SET_PV2 uses temp */
			break;

		case 0x05:      /* DEC B */
			BC -= 0x100;
			temp = HIGH_REGISTER(BC);
			AF = (AF & ~0xfe) | decTable[temp] | SET_PV2(0x7f); /* SET_PV2 uses temp */
			break;

		case 0x06:      /* LD B,nn */
			SET_HIGH_REGISTER(BC, RAM_PP(PC));
			break;

		case 0x07:      /* RLCA */
			AF = ((AF >> 7) & 0x0128) | ((AF << 1) & ~0x1ff) |
				(AF & 0xc4) | ((AF >> 15) & 1);
			break;

		case 0x08:      /* EX AF,AF' */
			temp = AF;
			AF = AF1;
			AF1 = temp;
			break;

		case 0x09:      /* ADD HL,BC */
			HL &= ADDRMASK;
			BC &= ADDRMASK;
			sum = HL + BC;
			AF = (AF & ~0x3b) | ((sum >> 8) & 0x28) | cbitsTable[(HL ^ BC ^ sum) >> 8];
			HL = sum;
			break;

		case 0x0a:      /* LD A,(BC) */
			SET_HIGH_REGISTER(AF, GET_BYTE(BC));
			break;

		case 0x0b:      /* DEC BC */
			--BC;
			break;

		case 0x0c:      /* INC C */
			temp = LOW_REGISTER(BC) + 1;
			SET_LOW_REGISTER(BC, temp);
			AF = (AF & ~0xfe) | incTable[temp] | SET_PV2(0x80);
			break;

		case 0x0d:      /* DEC C */
			temp = LOW_REGISTER(BC) - 1;
			SET_LOW_REGISTER(BC, temp);
			AF = (AF & ~0xfe) | decTable[temp & 0xff] | SET_PV2(0x7f);
			break;

		case 0x0e:      /* LD C,nn */
			SET_LOW_REGISTER(BC, RAM_PP(PC));
			break;

		case 0x0f:      /* RRCA */
			AF = (AF & 0xc4) | rrcaTable[HIGH_REGISTER(AF)];
			break;

		case 0x10:      /* DJNZ dd */
			if ((BC -= 0x100) & 0xff00)
				PC += (int8)GET_BYTE(PC) + 1;
			else
				++PC;
			break;

		case 0x11:      /* LD DE,nnnn */
			DE = GET_WORD(PC);
			PC += 2;
			break;

		case 0x12:      /* LD (DE),A */
			PUT_BYTE(DE, HIGH_REGISTER(AF));
			break;

		case 0x13:      /* INC DE */
			++DE;
			break;

		case 0x14:      /* INC D */
			DE += 0x100;
			temp = HIGH_REGISTER(DE);
			AF = (AF & ~0xfe) | incTable[temp] | SET_PV2(0x80); /* SET_PV2 uses temp */
			break;

		case 0x15:      /* DEC D */
			DE -= 0x100;
			temp = HIGH_REGISTER(DE);
			AF = (AF & ~0xfe) | decTable[temp] | SET_PV2(0x7f); /* SET_PV2 uses temp */
			break;

		case 0x16:      /* LD D,nn */
			SET_HIGH_REGISTER(DE, RAM_PP(PC));
			break;

		case 0x17:      /* RLA */
			AF = ((AF << 8) & 0x0100) | ((AF >> 7) & 0x28) | ((AF << 1) & ~0x01ff) |
				(AF & 0xc4) | ((AF >> 15) & 1);
			break;

		case 0x18:      /* JR dd */
			PC += (int8)GET_BYTE(PC) + 1;
			break;

		case 0x19:      /* ADD HL,DE */
			HL &= ADDRMASK;
			DE &= ADDRMASK;
			sum = HL + DE;
			AF = (AF & ~0x3b) | ((sum >> 8) & 0x28) | cbitsTable[(HL ^ DE ^ sum) >> 8];
			HL = sum;
			break;

		case 0x1a:      /* LD A,(DE) */
			SET_HIGH_REGISTER(AF, GET_BYTE(DE));
			break;

		case 0x1b:      /* DEC DE */
			--DE;
			break;

		case 0x1c:      /* INC E */
			temp = LOW_REGISTER(DE) + 1;
			SET_LOW_REGISTER(DE, temp);
			AF = (AF & ~0xfe) | incTable[temp] | SET_PV2(0x80);
			break;

		case 0x1d:      /* DEC E */
			temp = LOW_REGISTER(DE) - 1;
			SET_LOW_REGISTER(DE, temp);
			AF = (AF & ~0xfe) | decTable[temp & 0xff] | SET_PV2(0x7f);
			break;

		case 0x1e:      /* LD E,nn */
			SET_LOW_REGISTER(DE, RAM_PP(PC));
			break;

		case 0x1f:      /* RRA */
			AF = ((AF & 1) << 15) | (AF & 0xc4) | rraTable[HIGH_REGISTER(AF)];
			break;

		case 0x20:      /* JR NZ,dd */
			if (TSTFLAG(Z))
				++PC;
			else
				PC += (int8)GET_BYTE(PC) + 1;
			break;

		case 0x21:      /* LD HL,nnnn */
			HL = GET_WORD(PC);
			PC += 2;
			break;

		case 0x22:      /* LD (nnnn),HL */
			temp = GET_WORD(PC);
			PUT_WORD(temp, HL);
			PC += 2;
			break;

		case 0x23:      /* INC HL */
			++HL;
			break;

		case 0x24:      /* INC H */
			HL += 0x100;
			temp = HIGH_REGISTER(HL);
			AF = (AF & ~0xfe) | incTable[temp] | SET_PV2(0x80); /* SET_PV2 uses temp */
			break;

		case 0x25:      /* DEC H */
			HL -= 0x100;
			temp = HIGH_REGISTER(HL);
			AF = (AF & ~0xfe) | decTable[temp] | SET_PV2(0x7f); /* SET_PV2 uses temp */
			break;

		case 0x26:      /* LD H,nn */
			SET_HIGH_REGISTER(HL, RAM_PP(PC));
			break;

		case 0x27:      /* DAA */
			acu = HIGH_REGISTER(AF);
			temp = LOW_DIGIT(acu);
			cbits = TSTFLAG(C);
			if (TSTFLAG(N)) {   /* last operation was a subtract */
				int hd = cbits || acu > 0x99;
				if (TSTFLAG(H) || (temp > 9)) { /* adjust low digit */
					if (temp > 5)
						SETFLAG(H, 0);
					acu -= 6;
					acu &= 0xff;
				}
				if (hd)
					acu -= 0x160;   /* adjust high digit */
			} else {          /* last operation was an add */
				if (TSTFLAG(H) || (temp > 9)) { /* adjust low digit */
					SETFLAG(H, (temp > 9));
					acu += 6;
				}
				if (cbits || ((acu & 0x1f0) > 0x90))
					acu += 0x60;   /* adjust high digit */
			}
			AF = (AF & 0x12) | rrdrldTable[acu & 0xff] | ((acu >> 8) & 1) | cbits;
			break;

		case 0x28:      /* JR Z,dd */
			if (TSTFLAG(Z))
				PC += (int8)GET_BYTE(PC) + 1;
			else
				++PC;
			break;

		case 0x29:      /* ADD HL,HL */
			HL &= ADDRMASK;
			sum = HL + HL;
			AF = (AF & ~0x3b) | cbitsDup16Table[sum >> 8];
			HL = sum;
			break;

		case 0x2a:      /* LD HL,(nnnn) */
			temp = GET_WORD(PC);
			HL = GET_WORD(temp);
			PC += 2;
			break;

		case 0x2b:      /* DEC HL */
			--HL;
			break;

		case 0x2c:      /* INC L */
			temp = LOW_REGISTER(HL) + 1;
			SET_LOW_REGISTER(HL, temp);
			AF = (AF & ~0xfe) | incTable[temp] | SET_PV2(0x80);
			break;

		case 0x2d:      /* DEC L */
			temp = LOW_REGISTER(HL) - 1;
			SET_LOW_REGISTER(HL, temp);
			AF = (AF & ~0xfe) | decTable[temp & 0xff] | SET_PV2(0x7f);
			break;

		case 0x2e:      /* LD L,nn */
			SET_LOW_REGISTER(HL, RAM_PP(PC));
			break;

		case 0x2f:      /* CPL */
			AF = (~AF & ~0xff) | (AF & 0xc5) | ((~AF >> 8) & 0x28) | 0x12;
			break;

		case 0x30:      /* JR NC,dd */
			if (TSTFLAG(C))
				++PC;
			else
				PC += (int8)GET_BYTE(PC) + 1;
			break;

		case 0x31:      /* LD SP,nnnn */
			SP = GET_WORD(PC);
			PC += 2;
			break;

		case 0x32:      /* LD (nnnn),A */
			temp = GET_WORD(PC);
			PUT_BYTE(temp, HIGH_REGISTER(AF));
			PC += 2;
			break;

		case 0x33:      /* INC SP */
			++SP;
			break;

		case 0x34:      /* INC (HL) */
			temp = GET_BYTE(HL) + 1;
			PUT_BYTE(HL, temp);
			AF = (AF & ~0xfe) | incTable[temp] | SET_PV2(0x80);
			break;

		case 0x35:      /* DEC (HL) */
			temp = GET_BYTE(HL) - 1;
			PUT_BYTE(HL, temp);
			AF = (AF & ~0xfe) | decTable[temp & 0xff] | SET_PV2(0x7f);
			break;

		case 0x36:      /* LD (HL),nn */
			PUT_BYTE(HL, RAM_PP(PC));
			break;

		case 0x37:      /* SCF */
			AF = (AF & ~0x3b) | ((AF >> 8) & 0x28) | 1;
			break;

		case 0x38:      /* JR C,dd */
			if (TSTFLAG(C))
				PC += (int8)GET_BYTE(PC) + 1;
			else
				++PC;
			break;

		case 0x39:      /* ADD HL,SP */
			HL &= ADDRMASK;
			SP &= ADDRMASK;
			sum = HL + SP;
			AF = (AF & ~0x3b) | ((sum >> 8) & 0x28) | cbitsTable[(HL ^ SP ^ sum) >> 8];
			HL = sum;
			break;

		case 0x3a:      /* LD A,(nnnn) */
			temp = GET_WORD(PC);
			SET_HIGH_REGISTER(AF, GET_BYTE(temp));
			PC += 2;
			break;

		case 0x3b:      /* DEC SP */
			--SP;
			break;

		case 0x3c:      /* INC A */
			AF += 0x100;
			temp = HIGH_REGISTER(AF);
			AF = (AF & ~0xfe) | incTable[temp] | SET_PV2(0x80); /* SET_PV2 uses temp */
			break;

		case 0x3d:      /* DEC A */
			AF -= 0x100;
			temp = HIGH_REGISTER(AF);
			AF = (AF & ~0xfe) | decTable[temp] | SET_PV2(0x7f); /* SET_PV2 uses temp */
			break;

		case 0x3e:      /* LD A,nn */
			SET_HIGH_REGISTER(AF, RAM_PP(PC));
			break;

		case 0x3f:      /* CCF */
			AF = (AF & ~0x3b) | ((AF >> 8) & 0x28) | ((AF & 1) << 4) | (~AF & 1);
			break;

		case 0x40:      /* LD B,B */
			break;

		case 0x41:      /* LD B,C */
			BC = (BC & 0xff) | ((BC & 0xff) << 8);
			break;

		case 0x42:      /* LD B,D */
			BC = (BC & 0xff) | (DE & ~0xff);
			break;

		case 0x43:      /* LD B,E */
			BC = (BC & 0xff) | ((DE & 0xff) << 8);
			break;

		case 0x44:      /* LD B,H */
			BC = (BC & 0xff) | (HL & ~0xff);
			break;

		case 0x45:      /* LD B,L */
			BC = (BC & 0xff) | ((HL & 0xff) << 8);
			break;

		case 0x46:      /* LD B,(HL) */
			SET_HIGH_REGISTER(BC, GET_BYTE(HL));
			break;

		case 0x47:      /* LD B,A */
			BC = (BC & 0xff) | (AF & ~0xff);
			break;

		case 0x48:      /* LD C,B */
			BC = (BC & ~0xff) | ((BC >> 8) & 0xff);
			break;

		case 0x49:      /* LD C,C */
			break;

		case 0x4a:      /* LD C,D */
			BC = (BC & ~0xff) | ((DE >> 8) & 0xff);
			break;

		case 0x4b:      /* LD C,E */
			BC = (BC & ~0xff) | (DE & 0xff);
			break;

		case 0x4c:      /* LD C,H */
			BC = (BC & ~0xff) | ((HL >> 8) & 0xff);
			break;

		case 0x4d:      /* LD C,L */
			BC = (BC & ~0xff) | (HL & 0xff);
			break;

		case 0x4e:      /* LD C,(HL) */
			SET_LOW_REGISTER(BC, GET_BYTE(HL));
			break;

		case 0x4f:      /* LD C,A */
			BC = (BC & ~0xff) | ((AF >> 8) & 0xff);
			break;

		case 0x50:      /* LD D,B */
			DE = (DE & 0xff) | (BC & ~0xff);
			break;

		case 0x51:      /* LD D,C */
			DE = (DE & 0xff) | ((BC & 0xff) << 8);
			break;

		case 0x52:      /* LD D,D */
			break;

		case 0x53:      /* LD D,E */
			DE = (DE & 0xff) | ((DE & 0xff) << 8);
			break;

		case 0x54:      /* LD D,H */
			DE = (DE & 0xff) | (HL & ~0xff);
			break;

		case 0x55:      /* LD D,L */
			DE = (DE & 0xff) | ((HL & 0xff) << 8);
			break;

		case 0x56:      /* LD D,(HL) */
			SET_HIGH_REGISTER(DE, GET_BYTE(HL));
			break;

		case 0x57:      /* LD D,A */
			DE = (DE & 0xff) | (AF & ~0xff);
			break;

		case 0x58:      /* LD E,B */
			DE = (DE & ~0xff) | ((BC >> 8) & 0xff);
			break;

		case 0x59:      /* LD E,C */
			DE = (DE & ~0xff) | (BC & 0xff);
			break;

		case 0x5a:      /* LD E,D */
			DE = (DE & ~0xff) | ((DE >> 8) & 0xff);
			break;

		case 0x5b:      /* LD E,E */
			break;

		case 0x5c:      /* LD E,H */
			DE = (DE & ~0xff) | ((HL >> 8) & 0xff);
			break;

		case 0x5d:      /* LD E,L */
			DE = (DE & ~0xff) | (HL & 0xff);
			break;

		case 0x5e:      /* LD E,(HL) */
			SET_LOW_REGISTER(DE, GET_BYTE(HL));
			break;

		case 0x5f:      /* LD E,A */
			DE = (DE & ~0xff) | ((AF >> 8) & 0xff);
			break;

		case 0x60:      /* LD H,B */
			HL = (HL & 0xff) | (BC & ~0xff);
			break;

		case 0x61:      /* LD H,C */
			HL = (HL & 0xff) | ((BC & 0xff) << 8);
			break;

		case 0x62:      /* LD H,D */
			HL = (HL & 0xff) | (DE & ~0xff);
			break;

		case 0x63:      /* LD H,E */
			HL = (HL & 0xff) | ((DE & 0xff) << 8);
			break;

		case 0x64:      /* LD H,H */
			break;

		case 0x65:      /* LD H,L */
			HL = (HL & 0xff) | ((HL & 0xff) << 8);
			break;

		case 0x66:      /* LD H,(HL) */
			SET_HIGH_REGISTER(HL, GET_BYTE(HL));
			break;

		case 0x67:      /* LD H,A */
			HL = (HL & 0xff) | (AF & ~0xff);
			break;

		case 0x68:      /* LD L,B */
			HL = (HL & ~0xff) | ((BC >> 8) & 0xff);
			break;

		case 0x69:      /* LD L,C */
			HL = (HL & ~0xff) | (BC & 0xff);
			break;

		case 0x6a:      /* LD L,D */
			HL = (HL & ~0xff) | ((DE >> 8) & 0xff);
			break;

		case 0x6b:      /* LD L,E */
			HL = (HL & ~0xff) | (DE & 0xff);
			break;

		case 0x6c:      /* LD L,H */
			HL = (HL & ~0xff) | ((HL >> 8) & 0xff);
			break;

		case 0x6d:      /* LD L,L */
			break;

		case 0x6e:      /* LD L,(HL) */
			SET_LOW_REGISTER(HL, GET_BYTE(HL));
			break;

		case 0x6f:      /* LD L,A */
			HL = (HL & ~0xff) | ((AF >> 8) & 0xff);
			break;

		case 0x70:      /* LD (HL),B */
			PUT_BYTE(HL, HIGH_REGISTER(BC));
			break;

		case 0x71:      /* LD (HL),C */
			PUT_BYTE(HL, LOW_REGISTER(BC));
			break;

		case 0x72:      /* LD (HL),D */
			PUT_BYTE(HL, HIGH_REGISTER(DE));
			break;

		case 0x73:      /* LD (HL),E */
			PUT_BYTE(HL, LOW_REGISTER(DE));
			break;

		case 0x74:      /* LD (HL),H */
			PUT_BYTE(HL, HIGH_REGISTER(HL));
			break;

		case 0x75:      /* LD (HL),L */
			PUT_BYTE(HL, LOW_REGISTER(HL));
			break;

		case 0x76:      /* HALT */
#ifdef DEBUG
			_puts("\r\n::CPU HALTED::");	// A halt is a good indicator of broken code
			_puts("Press any key...");
			_getch();
#endif
			--PC;
			goto end_decode;
			break;

		case 0x77:      /* LD (HL),A */
			PUT_BYTE(HL, HIGH_REGISTER(AF));
			break;

		case 0x78:      /* LD A,B */
			AF = (AF & 0xff) | (BC & ~0xff);
			break;

		case 0x79:      /* LD A,C */
			AF = (AF & 0xff) | ((BC & 0xff) << 8);
			break;

		case 0x7a:      /* LD A,D */
			AF = (AF & 0xff) | (DE & ~0xff);
			break;

		case 0x7b:      /* LD A,E */
			AF = (AF & 0xff) | ((DE & 0xff) << 8);
			break;

		case 0x7c:      /* LD A,H */
			AF = (AF & 0xff) | (HL & ~0xff);
			break;

		case 0x7d:      /* LD A,L */
			AF = (AF & 0xff) | ((HL & 0xff) << 8);
			break;

		case 0x7e:      /* LD A,(HL) */
			SET_HIGH_REGISTER(AF, GET_BYTE(HL));
			break;

		case 0x7f:      /* LD A,A */
			break;

		case 0x80:      /* ADD A,B */
			temp = HIGH_REGISTER(BC);
			acu = HIGH_REGISTER(AF);
			sum = acu + temp;
			cbits = acu ^ temp ^ sum;
			AF = addTable[sum] | cbitsTable[cbits] | (SET_PV);
			break;

		case 0x81:      /* ADD A,C */
			temp = LOW_REGISTER(BC);
			acu = HIGH_REGISTER(AF);
			sum = acu + temp;
			cbits = acu ^ temp ^ sum;
			AF = addTable[sum] | cbitsTable[cbits] | (SET_PV);
			break;

		case 0x82:      /* ADD A,D */
			temp = HIGH_REGISTER(DE);
			acu = HIGH_REGISTER(AF);
			sum = acu + temp;
			cbits = acu ^ temp ^ sum;
			AF = addTable[sum] | cbitsTable[cbits] | (SET_PV);
			break;

		case 0x83:      /* ADD A,E */
			temp = LOW_REGISTER(DE);
			acu = HIGH_REGISTER(AF);
			sum = acu + temp;
			cbits = acu ^ temp ^ sum;
			AF = addTable[sum] | cbitsTable[cbits] | (SET_PV);
			break;

		case 0x84:      /* ADD A,H */
			temp = HIGH_REGISTER(HL);
			acu = HIGH_REGISTER(AF);
			sum = acu + temp;
			cbits = acu ^ temp ^ sum;
			AF = addTable[sum] | cbitsTable[cbits] | (SET_PV);
			break;

		case 0x85:      /* ADD A,L */
			temp = LOW_REGISTER(HL);
			acu = HIGH_REGISTER(AF);
			sum = acu + temp;
			cbits = acu ^ temp ^ sum;
			AF = addTable[sum] | cbitsTable[cbits] | (SET_PV);
			break;

		case 0x86:      /* ADD A,(HL) */
			temp = GET_BYTE(HL);
			acu = HIGH_REGISTER(AF);
			sum = acu + temp;
			cbits = acu ^ temp ^ sum;
			AF = addTable[sum] | cbitsTable[cbits] | (SET_PV);
			break;

		case 0x87:      /* ADD A,A */
			cbits = 2 * HIGH_REGISTER(AF);
			AF = cbitsDup8Table[cbits] | (SET_PVS(cbits));
			break;

		case 0x88:      /* ADC A,B */
			temp = HIGH_REGISTER(BC);
			acu = HIGH_REGISTER(AF);
			sum = acu + temp + TSTFLAG(C);
			cbits = acu ^ temp ^ sum;
			AF = addTable[sum] | cbitsTable[cbits] | (SET_PV);
			break;

		case 0x89:      /* ADC A,C */
			temp = LOW_REGISTER(BC);
			acu = HIGH_REGISTER(AF);
			sum = acu + temp + TSTFLAG(C);
			cbits = acu ^ temp ^ sum;
			AF = addTable[sum] | cbitsTable[cbits] | (SET_PV);
			break;

		case 0x8a:      /* ADC A,D */
			temp = HIGH_REGISTER(DE);
			acu = HIGH_REGISTER(AF);
			sum = acu + temp + TSTFLAG(C);
			cbits = acu ^ temp ^ sum;
			AF = addTable[sum] | cbitsTable[cbits] | (SET_PV);
			break;

		case 0x8b:      /* ADC A,E */
			temp = LOW_REGISTER(DE);
			acu = HIGH_REGISTER(AF);
			sum = acu + temp + TSTFLAG(C);
			cbits = acu ^ temp ^ sum;
			AF = addTable[sum] | cbitsTable[cbits] | (SET_PV);
			break;

		case 0x8c:      /* ADC A,H */
			temp = HIGH_REGISTER(HL);
			acu = HIGH_REGISTER(AF);
			sum = acu + temp + TSTFLAG(C);
			cbits = acu ^ temp ^ sum;
			AF = addTable[sum] | cbitsTable[cbits] | (SET_PV);
			break;

		case 0x8d:      /* ADC A,L */
			temp = LOW_REGISTER(HL);
			acu = HIGH_REGISTER(AF);
			sum = acu + temp + TSTFLAG(C);
			cbits = acu ^ temp ^ sum;
			AF = addTable[sum] | cbitsTable[cbits] | (SET_PV);
			break;

		case 0x8e:      /* ADC A,(HL) */
			temp = GET_BYTE(HL);
			acu = HIGH_REGISTER(AF);
			sum = acu + temp + TSTFLAG(C);
			cbits = acu ^ temp ^ sum;
			AF = addTable[sum] | cbitsTable[cbits] | (SET_PV);
			break;

		case 0x8f:      /* ADC A,A */
			cbits = 2 * HIGH_REGISTER(AF) + TSTFLAG(C);
			AF = cbitsDup8Table[cbits] | (SET_PVS(cbits));
			break;

		case 0x90:      /* SUB B */
			temp = HIGH_REGISTER(BC);
			acu = HIGH_REGISTER(AF);
			sum = acu - temp;
			cbits = acu ^ temp ^ sum;
			AF = subTable[sum & 0xff] | cbitsTable[cbits & 0x1ff] | (SET_PV);
			break;

		case 0x91:      /* SUB C */
			temp = LOW_REGISTER(BC);
			acu = HIGH_REGISTER(AF);
			sum = acu - temp;
			cbits = acu ^ temp ^ sum;
			AF = subTable[sum & 0xff] | cbitsTable[cbits & 0x1ff] | (SET_PV);
			break;

		case 0x92:      /* SUB D */
			temp = HIGH_REGISTER(DE);
			acu = HIGH_REGISTER(AF);
			sum = acu - temp;
			cbits = acu ^ temp ^ sum;
			AF = subTable[sum & 0xff] | cbitsTable[cbits & 0x1ff] | (SET_PV);
			break;

		case 0x93:      /* SUB E */
			temp = LOW_REGISTER(DE);
			acu = HIGH_REGISTER(AF);
			sum = acu - temp;
			cbits = acu ^ temp ^ sum;
			AF = subTable[sum & 0xff] | cbitsTable[cbits & 0x1ff] | (SET_PV);
			break;

		case 0x94:      /* SUB H */
			temp = HIGH_REGISTER(HL);
			acu = HIGH_REGISTER(AF);
			sum = acu - temp;
			cbits = acu ^ temp ^ sum;
			AF = subTable[sum & 0xff] | cbitsTable[cbits & 0x1ff] | (SET_PV);
			break;

		case 0x95:      /* SUB L */
			temp = LOW_REGISTER(HL);
			acu = HIGH_REGISTER(AF);
			sum = acu - temp;
			cbits = acu ^ temp ^ sum;
			AF = subTable[sum & 0xff] | cbitsTable[cbits & 0x1ff] | (SET_PV);
			break;

		case 0x96:      /* SUB (HL) */
			temp = GET_BYTE(HL);
			acu = HIGH_REGISTER(AF);
			sum = acu - temp;
			cbits = acu ^ temp ^ sum;
			AF = subTable[sum & 0xff] | cbitsTable[cbits & 0x1ff] | (SET_PV);
			break;

		case 0x97:      /* SUB A */
			AF = 0x42;
			break;

		case 0x98:      /* SBC A,B */
			temp = HIGH_REGISTER(BC);
			acu = HIGH_REGISTER(AF);
			sum = acu - temp - TSTFLAG(C);
			cbits = acu ^ temp ^ sum;
			AF = subTable[sum & 0xff] | cbitsTable[cbits & 0x1ff] | (SET_PV);
			break;

		case 0x99:      /* SBC A,C */
			temp = LOW_REGISTER(BC);
			acu = HIGH_REGISTER(AF);
			sum = acu - temp - TSTFLAG(C);
			cbits = acu ^ temp ^ sum;
			AF = subTable[sum & 0xff] | cbitsTable[cbits & 0x1ff] | (SET_PV);
			break;

		case 0x9a:      /* SBC A,D */
			temp = HIGH_REGISTER(DE);
			acu = HIGH_REGISTER(AF);
			sum = acu - temp - TSTFLAG(C);
			cbits = acu ^ temp ^ sum;
			AF = subTable[sum & 0xff] | cbitsTable[cbits & 0x1ff] | (SET_PV);
			break;

		case 0x9b:      /* SBC A,E */
			temp = LOW_REGISTER(DE);
			acu = HIGH_REGISTER(AF);
			sum = acu - temp - TSTFLAG(C);
			cbits = acu ^ temp ^ sum;
			AF = subTable[sum & 0xff] | cbitsTable[cbits & 0x1ff] | (SET_PV);
			break;

		case 0x9c:      /* SBC A,H */
			temp = HIGH_REGISTER(HL);
			acu = HIGH_REGISTER(AF);
			sum = acu - temp - TSTFLAG(C);
			cbits = acu ^ temp ^ sum;
			AF = subTable[sum & 0xff] | cbitsTable[cbits & 0x1ff] | (SET_PV);
			break;

		case 0x9d:      /* SBC A,L */
			temp = LOW_REGISTER(HL);
			acu = HIGH_REGISTER(AF);
			sum = acu - temp - TSTFLAG(C);
			cbits = acu ^ temp ^ sum;
			AF = subTable[sum & 0xff] | cbitsTable[cbits & 0x1ff] | (SET_PV);
			break;

		case 0x9e:      /* SBC A,(HL) */
			temp = GET_BYTE(HL);
			acu = HIGH_REGISTER(AF);
			sum = acu - temp - TSTFLAG(C);
			cbits = acu ^ temp ^ sum;
			AF = subTable[sum & 0xff] | cbitsTable[cbits & 0x1ff] | (SET_PV);
			break;

		case 0x9f:      /* SBC A,A */
			cbits = -TSTFLAG(C);
			AF = subTable[cbits & 0xff] | cbitsTable[cbits & 0x1ff] | (SET_PVS(cbits));
			break;

		case 0xa0:      /* AND B */
			AF = andTable[((AF & BC) >> 8) & 0xff];
			break;

		case 0xa1:      /* AND C */
			AF = andTable[((AF >> 8) & BC) & 0xff];
			break;

		case 0xa2:      /* AND D */
			AF = andTable[((AF & DE) >> 8) & 0xff];
			break;

		case 0xa3:      /* AND E */
			AF = andTable[((AF >> 8) & DE) & 0xff];
			break;

		case 0xa4:      /* AND H */
			AF = andTable[((AF & HL) >> 8) & 0xff];
			break;

		case 0xa5:      /* AND L */
			AF = andTable[((AF >> 8) & HL) & 0xff];
			break;

		case 0xa6:      /* AND (HL) */
			AF = andTable[((AF >> 8) & GET_BYTE(HL)) & 0xff];
			break;

		case 0xa7:      /* AND A */
			AF = andTable[(AF >> 8) & 0xff];
			break;

		case 0xa8:      /* XOR B */
			AF = xororTable[((AF ^ BC) >> 8) & 0xff];
			break;

		case 0xa9:      /* XOR C */
			AF = xororTable[((AF >> 8) ^ BC) & 0xff];
			break;

		case 0xaa:      /* XOR D */
			AF = xororTable[((AF ^ DE) >> 8) & 0xff];
			break;

		case 0xab:      /* XOR E */
			AF = xororTable[((AF >> 8) ^ DE) & 0xff];
			break;

		case 0xac:      /* XOR H */
			AF = xororTable[((AF ^ HL) >> 8) & 0xff];
			break;

		case 0xad:      /* XOR L */
			AF = xororTable[((AF >> 8) ^ HL) & 0xff];
			break;

		case 0xae:      /* XOR (HL) */
			AF = xororTable[((AF >> 8) ^ GET_BYTE(HL)) & 0xff];
			break;

		case 0xaf:      /* XOR A */
			AF = 0x44;
			break;

		case 0xb0:      /* OR B */
			AF = xororTable[((AF | BC) >> 8) & 0xff];
			break;

		case 0xb1:      /* OR C */
			AF = xororTable[((AF >> 8) | BC) & 0xff];
			break;

		case 0xb2:      /* OR D */
			AF = xororTable[((AF | DE) >> 8) & 0xff];
			break;

		case 0xb3:      /* OR E */
			AF = xororTable[((AF >> 8) | DE) & 0xff];
			break;

		case 0xb4:      /* OR H */
			AF = xororTable[((AF | HL) >> 8) & 0xff];
			break;

		case 0xb5:      /* OR L */
			AF = xororTable[((AF >> 8) | HL) & 0xff];
			break;

		case 0xb6:      /* OR (HL) */
			AF = xororTable[((AF >> 8) | GET_BYTE(HL)) & 0xff];
			break;

		case 0xb7:      /* OR A */
			AF = xororTable[(AF >> 8) & 0xff];
			break;

		case 0xb8:      /* CP B */
			temp = HIGH_REGISTER(BC);
			AF = (AF & ~0x28) | (temp & 0x28);
			acu = HIGH_REGISTER(AF);
			sum = acu - temp;
			cbits = acu ^ temp ^ sum;
			AF = (AF & ~0xff) | cpTable[sum & 0xff] | (temp & 0x28) |
				(SET_PV) | cbits2Table[cbits & 0x1ff];
			break;

		case 0xb9:      /* CP C */
			temp = LOW_REGISTER(BC);
			AF = (AF & ~0x28) | (temp & 0x28);
			acu = HIGH_REGISTER(AF);
			sum = acu - temp;
			cbits = acu ^ temp ^ sum;
			AF = (AF & ~0xff) | cpTable[sum & 0xff] | (temp & 0x28) |
				(SET_PV) | cbits2Table[cbits & 0x1ff];
			break;

		case 0xba:      /* CP D */
			temp = HIGH_REGISTER(DE);
			AF = (AF & ~0x28) | (temp & 0x28);
			acu = HIGH_REGISTER(AF);
			sum = acu - temp;
			cbits = acu ^ temp ^ sum;
			AF = (AF & ~0xff) | cpTable[sum & 0xff] | (temp & 0x28) |
				(SET_PV) | cbits2Table[cbits & 0x1ff];
			break;

		case 0xbb:      /* CP E */
			temp = LOW_REGISTER(DE);
			AF = (AF & ~0x28) | (temp & 0x28);
			acu = HIGH_REGISTER(AF);
			sum = acu - temp;
			cbits = acu ^ temp ^ sum;
			AF = (AF & ~0xff) | cpTable[sum & 0xff] | (temp & 0x28) |
				(SET_PV) | cbits2Table[cbits & 0x1ff];
			break;

		case 0xbc:      /* CP H */
			temp = HIGH_REGISTER(HL);
			AF = (AF & ~0x28) | (temp & 0x28);
			acu = HIGH_REGISTER(AF);
			sum = acu - temp;
			cbits = acu ^ temp ^ sum;
			AF = (AF & ~0xff) | cpTable[sum & 0xff] | (temp & 0x28) |
				(SET_PV) | cbits2Table[cbits & 0x1ff];
			break;

		case 0xbd:      /* CP L */
			temp = LOW_REGISTER(HL);
			AF = (AF & ~0x28) | (temp & 0x28);
			acu = HIGH_REGISTER(AF);
			sum = acu - temp;
			cbits = acu ^ temp ^ sum;
			AF = (AF & ~0xff) | cpTable[sum & 0xff] | (temp & 0x28) |
				(SET_PV) | cbits2Table[cbits & 0x1ff];
			break;

		case 0xbe:      /* CP (HL) */
			temp = GET_BYTE(HL);
			AF = (AF & ~0x28) | (temp & 0x28);
			acu = HIGH_REGISTER(AF);
			sum = acu - temp;
			cbits = acu ^ temp ^ sum;
			AF = (AF & ~0xff) | cpTable[sum & 0xff] | (temp & 0x28) |
				(SET_PV) | cbits2Table[cbits & 0x1ff];
			break;

		case 0xbf:      /* CP A */
			SET_LOW_REGISTER(AF, (HIGH_REGISTER(AF) & 0x28) | 0x42);
			break;

		case 0xc0:      /* RET NZ */
			if (!(TSTFLAG(Z)))
				POP(PC);
			break;

		case 0xc1:      /* POP BC */
			POP(BC);
			break;

		case 0xc2:      /* JP NZ,nnnn */
			JPC(!TSTFLAG(Z));
			break;

		case 0xc3:      /* JP nnnn */
			JPC(1);
			break;

		case 0xc4:      /* CALL NZ,nnnn */
			CALLC(!TSTFLAG(Z));
			break;

		case 0xc5:      /* PUSH BC */
			PUSH(BC);
			break;

		case 0xc6:      /* ADD A,nn */
			temp = RAM_PP(PC);
			acu = HIGH_REGISTER(AF);
			sum = acu + temp;
			cbits = acu ^ temp ^ sum;
			AF = addTable[sum] | cbitsTable[cbits] | (SET_PV);
			break;

		case 0xc7:      /* RST 0 */
			PUSH(PC);
			PC = 0;
			break;

		case 0xc8:      /* RET Z */
			if (TSTFLAG(Z))
				POP(PC);
			break;

		case 0xc9:      /* RET */
			POP(PC);
			break;

		case 0xca:      /* JP Z,nnnn */
			JPC(TSTFLAG(Z));
			break;

		case 0xcb:      /* CB prefix */
			adr = HL;
			acu = 0;
			switch ((op = GET_BYTE(PC)) & 7) {

			case 0:
				++PC;
				acu = HIGH_REGISTER(BC);
				break;

			case 1:
				++PC;
				acu = LOW_REGISTER(BC);
				break;

			case 2:
				++PC;
				acu = HIGH_REGISTER(DE);
				break;

			case 3:
				++PC;
				acu = LOW_REGISTER(DE);
				break;

			case 4:
				++PC;
				acu = HIGH_REGISTER(HL);
				break;

			case 5:
				++PC;
				acu = LOW_REGISTER(HL);
				break;

			case 6:
				++PC;
				acu = GET_BYTE(adr);
				break;

			case 7:
				++PC;
				acu = HIGH_REGISTER(AF);
				break;
			}
			switch (op & 0xc0) {

			case 0x00:  /* shift/rotate */
				switch (op & 0x38) {

				case 0x00:/* RLC */
					temp = (acu << 1) | (acu >> 7);
					cbits = temp & 1;
					goto cbshflg1;

				case 0x08:/* RRC */
					temp = (acu >> 1) | (acu << 7);
					cbits = temp & 0x80;
					goto cbshflg1;

				case 0x10:/* RL */
					temp = (acu << 1) | TSTFLAG(C);
					cbits = acu & 0x80;
					goto cbshflg1;

				case 0x18:/* RR */
					temp = (acu >> 1) | (TSTFLAG(C) << 7);
					cbits = acu & 1;
					goto cbshflg1;

				case 0x20:/* SLA */
					temp = acu << 1;
					cbits = acu & 0x80;
					goto cbshflg1;

				case 0x28:/* SRA */
					temp = (acu >> 1) | (acu & 0x80);
					cbits = acu & 1;
					goto cbshflg1;

				case 0x30:/* SLIA */
					temp = (acu << 1) | 1;
					cbits = acu & 0x80;
					goto cbshflg1;

				case 0x38:/* SRL */
					temp = acu >> 1;
					cbits = acu & 1;
				cbshflg1:
					AF = (AF & ~0xff) | rotateShiftTable[temp & 0xff] | !!cbits;
				}
				break;

			case 0x40:  /* BIT */
				if (acu & (1 << ((op >> 3) & 7)))
					AF = (AF & ~0xfe) | 0x10 | (((op & 0x38) == 0x38) << 7);
				else
					AF = (AF & ~0xfe) | 0x54;
				if ((op & 7) != 6)
					AF |= (acu & 0x28);
				temp = acu;
				break;

			case 0x80:  /* RES */
				temp = acu & ~(1 << ((op >> 3) & 7));
				break;

			case 0xc0:  /* SET */
				temp = acu | (1 << ((op >> 3) & 7));
				break;
			}
			switch (op & 7) {

			case 0:
				SET_HIGH_REGISTER(BC, temp);
				break;

			case 1:
				SET_LOW_REGISTER(BC, temp);
				break;

			case 2:
				SET_HIGH_REGISTER(DE, temp);
				break;

			case 3:
				SET_LOW_REGISTER(DE, temp);
				break;

			case 4:
				SET_HIGH_REGISTER(HL, temp);
				break;

			case 5:
				SET_LOW_REGISTER(HL, temp);
				break;

			case 6:
				PUT_BYTE(adr, temp);
				break;

			case 7:
				SET_HIGH_REGISTER(AF, temp);
				break;
			}
			break;

		case 0xcc:      /* CALL Z,nnnn */
			CALLC(TSTFLAG(Z));
			break;

		case 0xcd:      /* CALL nnnn */
			CALLC(1);
			break;

		case 0xce:      /* ADC A,nn */
			temp = RAM_PP(PC);
			acu = HIGH_REGISTER(AF);
			sum = acu + temp + TSTFLAG(C);
			cbits = acu ^ temp ^ sum;
			AF = addTable[sum] | cbitsTable[cbits] | (SET_PV);
			break;

		case 0xcf:      /* RST 8 */
			PUSH(PC);
			PC = 8;
			break;

		case 0xd0:      /* RET NC */
			if (!(TSTFLAG(C)))
				POP(PC);
			break;

		case 0xd1:      /* POP DE */
			POP(DE);
			break;

		case 0xd2:      /* JP NC,nnnn */
			JPC(!TSTFLAG(C));
			break;

		case 0xd3:      /* OUT (nn),A */
			cpu_out(RAM_PP(PC), HIGH_REGISTER(AF));
			break;

		case 0xd4:      /* CALL NC,nnnn */
			CALLC(!TSTFLAG(C));
			break;

		case 0xd5:      /* PUSH DE */
			PUSH(DE);
			break;

		case 0xd6:      /* SUB nn */
			temp = RAM_PP(PC);
			acu = HIGH_REGISTER(AF);
			sum = acu - temp;
			cbits = acu ^ temp ^ sum;
			AF = subTable[sum & 0xff] | cbitsTable[cbits & 0x1ff] | (SET_PV);
			break;

		case 0xd7:      /* RST 10H */
			PUSH(PC);
			PC = 0x10;
			break;

		case 0xd8:      /* RET C */
			if (TSTFLAG(C))
				POP(PC);
			break;

		case 0xd9:      /* EXX */
			temp = BC;
			BC = BC1;
			BC1 = temp;
			temp = DE;
			DE = DE1;
			DE1 = temp;
			temp = HL;
			HL = HL1;
			HL1 = temp;
			break;

		case 0xda:      /* JP C,nnnn */
			JPC(TSTFLAG(C));
			break;

		case 0xdb:      /* IN A,(nn) */
			SET_HIGH_REGISTER(AF, cpu_in(RAM_PP(PC)));
			break;

		case 0xdc:      /* CALL C,nnnn */
			CALLC(TSTFLAG(C));
			break;

		case 0xdd:      /* DD prefix */
			switch (RAM_PP(PC)) {

			case 0x09:      /* ADD IX,BC */
				IX &= ADDRMASK;
				BC &= ADDRMASK;
				sum = IX + BC;
				AF = (AF & ~0x3b) | ((sum >> 8) & 0x28) | cbitsTable[(IX ^ BC ^ sum) >> 8];
				IX = sum;
				break;

			case 0x19:      /* ADD IX,DE */
				IX &= ADDRMASK;
				DE &= ADDRMASK;
				sum = IX + DE;
				AF = (AF & ~0x3b) | ((sum >> 8) & 0x28) | cbitsTable[(IX ^ DE ^ sum) >> 8];
				IX = sum;
				break;

			case 0x21:      /* LD IX,nnnn */
				IX = GET_WORD(PC);
				PC += 2;
				break;

			case 0x22:      /* LD (nnnn),IX */
				temp = GET_WORD(PC);
				PUT_WORD(temp, IX);
				PC += 2;
				break;

			case 0x23:      /* INC IX */
				++IX;
				break;

			case 0x24:      /* INC IXH */
				IX += 0x100;
				AF = (AF & ~0xfe) | incZ80Table[HIGH_REGISTER(IX)];
				break;

			case 0x25:      /* DEC IXH */
				IX -= 0x100;
				AF = (AF & ~0xfe) | decZ80Table[HIGH_REGISTER(IX)];
				break;

			case 0x26:      /* LD IXH,nn */
				SET_HIGH_REGISTER(IX, RAM_PP(PC));
				break;

			case 0x29:      /* ADD IX,IX */
				IX &= ADDRMASK;
				sum = IX + IX;
				AF = (AF & ~0x3b) | cbitsDup16Table[sum >> 8];
				IX = sum;
				break;

			case 0x2a:      /* LD IX,(nnnn) */
				temp = GET_WORD(PC);
				IX = GET_WORD(temp);
				PC += 2;
				break;

			case 0x2b:      /* DEC IX */
				--IX;
				break;

			case 0x2c:      /* INC IXL */
				temp = LOW_REGISTER(IX) + 1;
				SET_LOW_REGISTER(IX, temp);
				AF = (AF & ~0xfe) | incZ80Table[temp];
				break;

			case 0x2d:      /* DEC IXL */
				temp = LOW_REGISTER(IX) - 1;
				SET_LOW_REGISTER(IX, temp);
				AF = (AF & ~0xfe) | decZ80Table[temp & 0xff];
				break;

			case 0x2e:      /* LD IXL,nn */
				SET_LOW_REGISTER(IX, RAM_PP(PC));
				break;

			case 0x34:      /* INC (IX+dd) */
				adr = IX + (int8)RAM_PP(PC);
				temp = GET_BYTE(adr) + 1;
				PUT_BYTE(adr, temp);
				AF = (AF & ~0xfe) | incZ80Table[temp];
				break;

			case 0x35:      /* DEC (IX+dd) */
				adr = IX + (int8)RAM_PP(PC);
				temp = GET_BYTE(adr) - 1;
				PUT_BYTE(adr, temp);
				AF = (AF & ~0xfe) | decZ80Table[temp & 0xff];
				break;

			case 0x36:      /* LD (IX+dd),nn */
				adr = IX + (int8)RAM_PP(PC);
				PUT_BYTE(adr, RAM_PP(PC));
				break;

			case 0x39:      /* ADD IX,SP */
				IX &= ADDRMASK;
				SP &= ADDRMASK;
				sum = IX + SP;
				AF = (AF & ~0x3b) | ((sum >> 8) & 0x28) | cbitsTable[(IX ^ SP ^ sum) >> 8];
				IX = sum;
				break;

			case 0x44:      /* LD B,IXH */
				SET_HIGH_REGISTER(BC, HIGH_REGISTER(IX));
				break;

			case 0x45:      /* LD B,IXL */
				SET_HIGH_REGISTER(BC, LOW_REGISTER(IX));
				break;

			case 0x46:      /* LD B,(IX+dd) */
				adr = IX + (int8)RAM_PP(PC);
				SET_HIGH_REGISTER(BC, GET_BYTE(adr));
				break;

			case 0x4c:      /* LD C,IXH */
				SET_LOW_REGISTER(BC, HIGH_REGISTER(IX));
				break;

			case 0x4d:      /* LD C,IXL */
				SET_LOW_REGISTER(BC, LOW_REGISTER(IX));
				break;

			case 0x4e:      /* LD C,(IX+dd) */
				adr = IX + (int8)RAM_PP(PC);
				SET_LOW_REGISTER(BC, GET_BYTE(adr));
				break;

			case 0x54:      /* LD D,IXH */
				SET_HIGH_REGISTER(DE, HIGH_REGISTER(IX));
				break;

			case 0x55:      /* LD D,IXL */
				SET_HIGH_REGISTER(DE, LOW_REGISTER(IX));
				break;

			case 0x56:      /* LD D,(IX+dd) */
				adr = IX + (int8)RAM_PP(PC);
				SET_HIGH_REGISTER(DE, GET_BYTE(adr));
				break;

			case 0x5c:      /* LD E,IXH */
				SET_LOW_REGISTER(DE, HIGH_REGISTER(IX));
				break;

			case 0x5d:      /* LD E,IXL */
				SET_LOW_REGISTER(DE, LOW_REGISTER(IX));
				break;

			case 0x5e:      /* LD E,(IX+dd) */
				adr = IX + (int8)RAM_PP(PC);
				SET_LOW_REGISTER(DE, GET_BYTE(adr));
				break;

			case 0x60:      /* LD IXH,B */
				SET_HIGH_REGISTER(IX, HIGH_REGISTER(BC));
				break;

			case 0x61:      /* LD IXH,C */
				SET_HIGH_REGISTER(IX, LOW_REGISTER(BC));
				break;

			case 0x62:      /* LD IXH,D */
				SET_HIGH_REGISTER(IX, HIGH_REGISTER(DE));
				break;

			case 0x63:      /* LD IXH,E */
				SET_HIGH_REGISTER(IX, LOW_REGISTER(DE));
				break;

			case 0x64:      /* LD IXH,IXH */
				break;

			case 0x65:      /* LD IXH,IXL */
				SET_HIGH_REGISTER(IX, LOW_REGISTER(IX));
				break;

			case 0x66:      /* LD H,(IX+dd) */
				adr = IX + (int8)RAM_PP(PC);
				SET_HIGH_REGISTER(HL, GET_BYTE(adr));
				break;

			case 0x67:      /* LD IXH,A */
				SET_HIGH_REGISTER(IX, HIGH_REGISTER(AF));
				break;

			case 0x68:      /* LD IXL,B */
				SET_LOW_REGISTER(IX, HIGH_REGISTER(BC));
				break;

			case 0x69:      /* LD IXL,C */
				SET_LOW_REGISTER(IX, LOW_REGISTER(BC));
				break;

			case 0x6a:      /* LD IXL,D */
				SET_LOW_REGISTER(IX, HIGH_REGISTER(DE));
				break;

			case 0x6b:      /* LD IXL,E */
				SET_LOW_REGISTER(IX, LOW_REGISTER(DE));
				break;

			case 0x6c:      /* LD IXL,IXH */
				SET_LOW_REGISTER(IX, HIGH_REGISTER(IX));
				break;

			case 0x6d:      /* LD IXL,IXL */
				break;

			case 0x6e:      /* LD L,(IX+dd) */
				adr = IX + (int8)RAM_PP(PC);
				SET_LOW_REGISTER(HL, GET_BYTE(adr));
				break;

			case 0x6f:      /* LD IXL,A */
				SET_LOW_REGISTER(IX, HIGH_REGISTER(AF));
				break;

			case 0x70:      /* LD (IX+dd),B */
				adr = IX + (int8)RAM_PP(PC);
				PUT_BYTE(adr, HIGH_REGISTER(BC));
				break;

			case 0x71:      /* LD (IX+dd),C */
				adr = IX + (int8)RAM_PP(PC);
				PUT_BYTE(adr, LOW_REGISTER(BC));
				break;

			case 0x72:      /* LD (IX+dd),D */
				adr = IX + (int8)RAM_PP(PC);
				PUT_BYTE(adr, HIGH_REGISTER(DE));
				break;

			case 0x73:      /* LD (IX+dd),E */
				adr = IX + (int8)RAM_PP(PC);
				PUT_BYTE(adr, LOW_REGISTER(DE));
				break;

			case 0x74:      /* LD (IX+dd),H */
				adr = IX + (int8)RAM_PP(PC);
				PUT_BYTE(adr, HIGH_REGISTER(HL));
				break;

			case 0x75:      /* LD (IX+dd),L */
				adr = IX + (int8)RAM_PP(PC);
				PUT_BYTE(adr, LOW_REGISTER(HL));
				break;

			case 0x77:      /* LD (IX+dd),A */
				adr = IX + (int8)RAM_PP(PC);
				PUT_BYTE(adr, HIGH_REGISTER(AF));
				break;

			case 0x7c:      /* LD A,IXH */
				SET_HIGH_REGISTER(AF, HIGH_REGISTER(IX));
				break;

			case 0x7d:      /* LD A,IXL */
				SET_HIGH_REGISTER(AF, LOW_REGISTER(IX));
				break;

			case 0x7e:      /* LD A,(IX+dd) */
				adr = IX + (int8)RAM_PP(PC);
				SET_HIGH_REGISTER(AF, GET_BYTE(adr));
				break;

			case 0x84:      /* ADD A,IXH */
				temp = HIGH_REGISTER(IX);
				acu = HIGH_REGISTER(AF);
				sum = acu + temp;
				AF = addTable[sum] | cbitsZ80Table[acu ^ temp ^ sum];
				break;

			case 0x85:      /* ADD A,IXL */
				temp = LOW_REGISTER(IX);
				acu = HIGH_REGISTER(AF);
				sum = acu + temp;
				AF = addTable[sum] | cbitsZ80Table[acu ^ temp ^ sum];
				break;

			case 0x86:      /* ADD A,(IX+dd) */
				adr = IX + (int8)RAM_PP(PC);
				temp = GET_BYTE(adr);
				acu = HIGH_REGISTER(AF);
				sum = acu + temp;
				AF = addTable[sum] | cbitsZ80Table[acu ^ temp ^ sum];
				break;

			case 0x8c:      /* ADC A,IXH */
				temp = HIGH_REGISTER(IX);
				acu = HIGH_REGISTER(AF);
				sum = acu + temp + TSTFLAG(C);
				AF = addTable[sum] | cbitsZ80Table[acu ^ temp ^ sum];
				break;

			case 0x8d:      /* ADC A,IXL */
				temp = LOW_REGISTER(IX);
				acu = HIGH_REGISTER(AF);
				sum = acu + temp + TSTFLAG(C);
				AF = addTable[sum] | cbitsZ80Table[acu ^ temp ^ sum];
				break;

			case 0x8e:      /* ADC A,(IX+dd) */
				adr = IX + (int8)RAM_PP(PC);
				temp = GET_BYTE(adr);
				acu = HIGH_REGISTER(AF);
				sum = acu + temp + TSTFLAG(C);
				AF = addTable[sum] | cbitsZ80Table[acu ^ temp ^ sum];
				break;

			case 0x96:      /* SUB (IX+dd) */
				adr = IX + (int8)RAM_PP(PC);
				temp = GET_BYTE(adr);
				acu = HIGH_REGISTER(AF);
				sum = acu - temp;
				AF = addTable[sum & 0xff] | cbits2Z80Table[(acu ^ temp ^ sum) & 0x1ff];
				break;

			case 0x94:      /* SUB IXH */
				SETFLAG(C, 0);/* fall through, a bit less efficient but smaller code */

			case 0x9c:      /* SBC A,IXH */
				temp = HIGH_REGISTER(IX);
				acu = HIGH_REGISTER(AF);
				sum = acu - temp - TSTFLAG(C);
				AF = addTable[sum & 0xff] | cbits2Z80Table[(acu ^ temp ^ sum) & 0x1ff];
				break;

			case 0x95:      /* SUB IXL */
				SETFLAG(C, 0);/* fall through, a bit less efficient but smaller code */

			case 0x9d:      /* SBC A,IXL */
				temp = LOW_REGISTER(IX);
				acu = HIGH_REGISTER(AF);
				sum = acu - temp - TSTFLAG(C);
				AF = addTable[sum & 0xff] | cbits2Z80Table[(acu ^ temp ^ sum) & 0x1ff];
				break;

			case 0x9e:      /* SBC A,(IX+dd) */
				adr = IX + (int8)RAM_PP(PC);
				temp = GET_BYTE(adr);
				acu = HIGH_REGISTER(AF);
				sum = acu - temp - TSTFLAG(C);
				AF = addTable[sum & 0xff] | cbits2Z80Table[(acu ^ temp ^ sum) & 0x1ff];
				break;

			case 0xa4:      /* AND IXH */
				AF = andTable[((AF & IX) >> 8) & 0xff];
				break;

			case 0xa5:      /* AND IXL */
				AF = andTable[((AF >> 8) & IX) & 0xff];
				break;

			case 0xa6:      /* AND (IX+dd) */
				adr = IX + (int8)RAM_PP(PC);
				AF = andTable[((AF >> 8) & GET_BYTE(adr)) & 0xff];
				break;

			case 0xac:      /* XOR IXH */
				AF = xororTable[((AF ^ IX) >> 8) & 0xff];
				break;

			case 0xad:      /* XOR IXL */
				AF = xororTable[((AF >> 8) ^ IX) & 0xff];
				break;

			case 0xae:      /* XOR (IX+dd) */
				adr = IX + (int8)RAM_PP(PC);
				AF = xororTable[((AF >> 8) ^ GET_BYTE(adr)) & 0xff];
				break;

			case 0xb4:      /* OR IXH */
				AF = xororTable[((AF | IX) >> 8) & 0xff];
				break;

			case 0xb5:      /* OR IXL */
				AF = xororTable[((AF >> 8) | IX) & 0xff];
				break;

			case 0xb6:      /* OR (IX+dd) */
				adr = IX + (int8)RAM_PP(PC);
				AF = xororTable[((AF >> 8) | GET_BYTE(adr)) & 0xff];
				break;

			case 0xbc:      /* CP IXH */
				temp = HIGH_REGISTER(IX);
				AF = (AF & ~0x28) | (temp & 0x28);
				acu = HIGH_REGISTER(AF);
				sum = acu - temp;
				AF = (AF & ~0xff) | cpTable[sum & 0xff] | (temp & 0x28) |
					cbits2Z80Table[(acu ^ temp ^ sum) & 0x1ff];
				break;

			case 0xbd:      /* CP IXL */
				temp = LOW_REGISTER(IX);
				AF = (AF & ~0x28) | (temp & 0x28);
				acu = HIGH_REGISTER(AF);
				sum = acu - temp;
				AF = (AF & ~0xff) | cpTable[sum & 0xff] | (temp & 0x28) |
					cbits2Z80Table[(acu ^ temp ^ sum) & 0x1ff];
				break;

			case 0xbe:      /* CP (IX+dd) */
				adr = IX + (int8)RAM_PP(PC);
				temp = GET_BYTE(adr);
				AF = (AF & ~0x28) | (temp & 0x28);
				acu = HIGH_REGISTER(AF);
				sum = acu - temp;
				AF = (AF & ~0xff) | cpTable[sum & 0xff] | (temp & 0x28) |
					cbits2Z80Table[(acu ^ temp ^ sum) & 0x1ff];
				break;

			case 0xcb:      /* CB prefix */
				adr = IX + (int8)RAM_PP(PC);
				acu = 0;
				switch ((op = GET_BYTE(PC)) & 7) {

				case 0:
					++PC;
					acu = HIGH_REGISTER(BC);
					break;

				case 1:
					++PC;
					acu = LOW_REGISTER(BC);
					break;

				case 2:
					++PC;
					acu = HIGH_REGISTER(DE);
					break;

				case 3:
					++PC;
					acu = LOW_REGISTER(DE);
					break;

				case 4:
					++PC;
					acu = HIGH_REGISTER(HL);
					break;

				case 5:
					++PC;
					acu = LOW_REGISTER(HL);
					break;

				case 6:
					++PC;
					acu = GET_BYTE(adr);
					break;

				case 7:
					++PC;
					acu = HIGH_REGISTER(AF);
					break;
				}
				switch (op & 0xc0) {

				case 0x00:  /* shift/rotate */
					switch (op & 0x38) {

					case 0x00:/* RLC */
						temp = (acu << 1) | (acu >> 7);
						cbits = temp & 1;
						goto cbshflg2;

					case 0x08:/* RRC */
						temp = (acu >> 1) | (acu << 7);
						cbits = temp & 0x80;
						goto cbshflg2;

					case 0x10:/* RL */
						temp = (acu << 1) | TSTFLAG(C);
						cbits = acu & 0x80;
						goto cbshflg2;

					case 0x18:/* RR */
						temp = (acu >> 1) | (TSTFLAG(C) << 7);
						cbits = acu & 1;
						goto cbshflg2;

					case 0x20:/* SLA */
						temp = acu << 1;
						cbits = acu & 0x80;
						goto cbshflg2;

					case 0x28:/* SRA */
						temp = (acu >> 1) | (acu & 0x80);
						cbits = acu & 1;
						goto cbshflg2;

					case 0x30:/* SLIA */
						temp = (acu << 1) | 1;
						cbits = acu & 0x80;
						goto cbshflg2;

					case 0x38:/* SRL */
						temp = acu >> 1;
						cbits = acu & 1;
					cbshflg2:
						AF = (AF & ~0xff) | rotateShiftTable[temp & 0xff] | !!cbits;
					}
					break;

				case 0x40:  /* BIT */
					if (acu & (1 << ((op >> 3) & 7)))
						AF = (AF & ~0xfe) | 0x10 | (((op & 0x38) == 0x38) << 7);
					else
						AF = (AF & ~0xfe) | 0x54;
					if ((op & 7) != 6)
						AF |= (acu & 0x28);
					temp = acu;
					break;

				case 0x80:  /* RES */
					temp = acu & ~(1 << ((op >> 3) & 7));
					break;

				case 0xc0:  /* SET */
					temp = acu | (1 << ((op >> 3) & 7));
					break;
				}
				switch (op & 7) {

				case 0:
					SET_HIGH_REGISTER(BC, temp);
					break;

				case 1:
					SET_LOW_REGISTER(BC, temp);
					break;

				case 2:
					SET_HIGH_REGISTER(DE, temp);
					break;

				case 3:
					SET_LOW_REGISTER(DE, temp);
					break;

				case 4:
					SET_HIGH_REGISTER(HL, temp);
					break;

				case 5:
					SET_LOW_REGISTER(HL, temp);
					break;

				case 6:
					PUT_BYTE(adr, temp);
					break;

				case 7:
					SET_HIGH_REGISTER(AF, temp);
					break;
				}
				break;

			case 0xe1:      /* POP IX */
				POP(IX);
				break;

			case 0xe3:      /* EX (SP),IX */
				temp = IX;
				POP(IX);
				PUSH(temp);
				break;

			case 0xe5:      /* PUSH IX */
				PUSH(IX);
				break;

			case 0xe9:      /* JP (IX) */
				PC = IX;
				break;

			case 0xf9:      /* LD SP,IX */
				SP = IX;
				break;

			default:                /* ignore DD */
				--PC;
			}
			break;

		case 0xde:          /* SBC A,nn */
			temp = RAM_PP(PC);
			acu = HIGH_REGISTER(AF);
			sum = acu - temp - TSTFLAG(C);
			cbits = acu ^ temp ^ sum;
			AF = subTable[sum & 0xff] | cbitsTable[cbits & 0x1ff] | (SET_PV);
			break;

		case 0xdf:      /* RST 18H */
			PUSH(PC);
			PC = 0x18;
			break;

		case 0xe0:      /* RET PO */
			if (!(TSTFLAG(P)))
				POP(PC);
			break;

		case 0xe1:      /* POP HL */
			POP(HL);
			break;

		case 0xe2:      /* JP PO,nnnn */
			JPC(!TSTFLAG(P));
			break;

		case 0xe3:      /* EX (SP),HL */
			temp = HL;
			POP(HL);
			PUSH(temp);
			break;

		case 0xe4:      /* CALL PO,nnnn */
			CALLC(!TSTFLAG(P));
			break;

		case 0xe5:      /* PUSH HL */
			PUSH(HL);
			break;

		case 0xe6:      /* AND nn */
			AF = andTable[((AF >> 8) & RAM_PP(PC)) & 0xff];
			break;

		case 0xe7:      /* RST 20H */
			PUSH(PC);
			PC = 0x20;
			break;

		case 0xe8:      /* RET PE */
			if (TSTFLAG(P))
				POP(PC);
			break;

		case 0xe9:      /* JP (HL) */
			PC = HL;
			break;

		case 0xea:      /* JP PE,nnnn */
			JPC(TSTFLAG(P));
			break;

		case 0xeb:      /* EX DE,HL */
			temp = HL;
			HL = DE;
			DE = temp;
			break;

		case 0xec:      /* CALL PE,nnnn */
			CALLC(TSTFLAG(P));
			break;

		case 0xed:      /* ED prefix */
			switch (RAM_PP(PC)) {

			case 0x40:      /* IN B,(C) */
				temp = cpu_in(LOW_REGISTER(BC));
				SET_HIGH_REGISTER(BC, temp);
				AF = (AF & ~0xfe) | rotateShiftTable[temp & 0xff];
				break;

			case 0x41:      /* OUT (C),B */
				cpu_out(LOW_REGISTER(BC), HIGH_REGISTER(BC));
				break;

			case 0x42:      /* SBC HL,BC */
				HL &= ADDRMASK;
				BC &= ADDRMASK;
				sum = HL - BC - TSTFLAG(C);
				AF = (AF & ~0xff) | ((sum >> 8) & 0xa8) | (((sum & ADDRMASK) == 0) << 6) |
					cbits2Z80Table[((HL ^ BC ^ sum) >> 8) & 0x1ff];
				HL = sum;
				break;

			case 0x43:      /* LD (nnnn),BC */
				temp = GET_WORD(PC);
				PUT_WORD(temp, BC);
				PC += 2;
				break;

			case 0x44:      /* NEG */

			case 0x4C:      /* NEG, unofficial */

			case 0x54:      /* NEG, unofficial */

			case 0x5C:      /* NEG, unofficial */

			case 0x64:      /* NEG, unofficial */

			case 0x6C:      /* NEG, unofficial */

			case 0x74:      /* NEG, unofficial */

			case 0x7C:      /* NEG, unofficial */
				temp = HIGH_REGISTER(AF);
				AF = ((~(AF & 0xff00) + 1) & 0xff00); /* AF = (-(AF & 0xff00) & 0xff00); */
				AF |= ((AF >> 8) & 0xa8) | (((AF & 0xff00) == 0) << 6) | negTable[temp];
				break;

			case 0x45:      /* RETN */

			case 0x55:      /* RETN, unofficial */

			case 0x5D:      /* RETN, unofficial */

			case 0x65:      /* RETN, unofficial */

			case 0x6D:      /* RETN, unofficial */

			case 0x75:      /* RETN, unofficial */

			case 0x7D:      /* RETN, unofficial */
				IFF |= IFF >> 1;
				POP(PC);
				break;

			case 0x46:      /* IM 0 */
							/* interrupt mode 0 */
				break;

			case 0x47:      /* LD I,A */
				IR = (IR & 0xff) | (AF & ~0xff);
				break;

			case 0x48:      /* IN C,(C) */
				temp = cpu_in(LOW_REGISTER(BC));
				SET_LOW_REGISTER(BC, temp);
				AF = (AF & ~0xfe) | rotateShiftTable[temp & 0xff];
				break;

			case 0x49:      /* OUT (C),C */
				cpu_out(LOW_REGISTER(BC), LOW_REGISTER(BC));
				break;

			case 0x4a:      /* ADC HL,BC */
				HL &= ADDRMASK;
				BC &= ADDRMASK;
				sum = HL + BC + TSTFLAG(C);
				AF = (AF & ~0xff) | ((sum >> 8) & 0xa8) | (((sum & ADDRMASK) == 0) << 6) |
					cbitsZ80Table[(HL ^ BC ^ sum) >> 8];
				HL = sum;
				break;

			case 0x4b:      /* LD BC,(nnnn) */
				temp = GET_WORD(PC);
				BC = GET_WORD(temp);
				PC += 2;
				break;

			case 0x4d:      /* RETI */
				IFF |= IFF >> 1;
				POP(PC);
				break;

			case 0x4f:      /* LD R,A */
				IR = (IR & ~0xff) | ((AF >> 8) & 0xff);
				break;

			case 0x50:      /* IN D,(C) */
				temp = cpu_in(LOW_REGISTER(BC));
				SET_HIGH_REGISTER(DE, temp);
				AF = (AF & ~0xfe) | rotateShiftTable[temp & 0xff];
				break;

			case 0x51:      /* OUT (C),D */
				cpu_out(LOW_REGISTER(BC), HIGH_REGISTER(DE));
				break;

			case 0x52:      /* SBC HL,DE */
				HL &= ADDRMASK;
				DE &= ADDRMASK;
				sum = HL - DE - TSTFLAG(C);
				AF = (AF & ~0xff) | ((sum >> 8) & 0xa8) | (((sum & ADDRMASK) == 0) << 6) |
					cbits2Z80Table[((HL ^ DE ^ sum) >> 8) & 0x1ff];
				HL = sum;
				break;

			case 0x53:      /* LD (nnnn),DE */
				temp = GET_WORD(PC);
				PUT_WORD(temp, DE);
				PC += 2;
				break;

			case 0x56:      /* IM 1 */
							/* interrupt mode 1 */
				break;

			case 0x57:      /* LD A,I */
				AF = (AF & 0x29) | (IR & ~0xff) | ((IR >> 8) & 0x80) | (((IR & ~0xff) == 0) << 6) | ((IFF & 2) << 1);
				break;

			case 0x58:      /* IN E,(C) */
				temp = cpu_in(LOW_REGISTER(BC));
				SET_LOW_REGISTER(DE, temp);
				AF = (AF & ~0xfe) | rotateShiftTable[temp & 0xff];
				break;

			case 0x59:      /* OUT (C),E */
				cpu_out(LOW_REGISTER(BC), LOW_REGISTER(DE));
				break;

			case 0x5a:      /* ADC HL,DE */
				HL &= ADDRMASK;
				DE &= ADDRMASK;
				sum = HL + DE + TSTFLAG(C);
				AF = (AF & ~0xff) | ((sum >> 8) & 0xa8) | (((sum & ADDRMASK) == 0) << 6) |
					cbitsZ80Table[(HL ^ DE ^ sum) >> 8];
				HL = sum;
				break;

			case 0x5b:      /* LD DE,(nnnn) */
				temp = GET_WORD(PC);
				DE = GET_WORD(temp);
				PC += 2;
				break;

			case 0x5e:      /* IM 2 */
							/* interrupt mode 2 */
				break;

			case 0x5f:      /* LD A,R */
				AF = (AF & 0x29) | ((IR & 0xff) << 8) | (IR & 0x80) |
					(((IR & 0xff) == 0) << 6) | ((IFF & 2) << 1);
				break;

			case 0x60:      /* IN H,(C) */
				temp = cpu_in(LOW_REGISTER(BC));
				SET_HIGH_REGISTER(HL, temp);
				AF = (AF & ~0xfe) | rotateShiftTable[temp & 0xff];
				break;

			case 0x61:      /* OUT (C),H */
				cpu_out(LOW_REGISTER(BC), HIGH_REGISTER(HL));
				break;

			case 0x62:      /* SBC HL,HL */
				HL &= ADDRMASK;
				sum = HL - HL - TSTFLAG(C);
				AF = (AF & ~0xff) | (((sum & ADDRMASK) == 0) << 6) |
					cbits2Z80DupTable[(sum >> 8) & 0x1ff];
				HL = sum;
				break;

			case 0x63:      /* LD (nnnn),HL */
				temp = GET_WORD(PC);
				PUT_WORD(temp, HL);
				PC += 2;
				break;

			case 0x67:      /* RRD */
				temp = GET_BYTE(HL);
				acu = HIGH_REGISTER(AF);
				PUT_BYTE(HL, HIGH_DIGIT(temp) | (LOW_DIGIT(acu) << 4));
				AF = rrdrldTable[(acu & 0xf0) | LOW_DIGIT(temp)] | (AF & 1);
				break;

			case 0x68:      /* IN L,(C) */
				temp = cpu_in(LOW_REGISTER(BC));
				SET_LOW_REGISTER(HL, temp);
				AF = (AF & ~0xfe) | rotateShiftTable[temp & 0xff];
				break;

			case 0x69:      /* OUT (C),L */
				cpu_out(LOW_REGISTER(BC), LOW_REGISTER(HL));
				break;

			case 0x6a:      /* ADC HL,HL */
				HL &= ADDRMASK;
				sum = HL + HL + TSTFLAG(C);
				AF = (AF & ~0xff) | (((sum & ADDRMASK) == 0) << 6) |
					cbitsZ80DupTable[sum >> 8];
				HL = sum;
				break;

			case 0x6b:      /* LD HL,(nnnn) */
				temp = GET_WORD(PC);
				HL = GET_WORD(temp);
				PC += 2;
				break;

			case 0x6f:      /* RLD */
				temp = GET_BYTE(HL);
				acu = HIGH_REGISTER(AF);
				PUT_BYTE(HL, (LOW_DIGIT(temp) << 4) | LOW_DIGIT(acu));
				AF = rrdrldTable[(acu & 0xf0) | HIGH_DIGIT(temp)] | (AF & 1);
				break;

			case 0x70:      /* IN (C) */
				temp = cpu_in(LOW_REGISTER(BC));
				SET_LOW_REGISTER(temp, temp);
				AF = (AF & ~0xfe) | rotateShiftTable[temp & 0xff];
				break;

			case 0x71:      /* OUT (C),0 */
				cpu_out(LOW_REGISTER(BC), 0);
				break;

			case 0x72:      /* SBC HL,SP */
				HL &= ADDRMASK;
				SP &= ADDRMASK;
				sum = HL - SP - TSTFLAG(C);
				AF = (AF & ~0xff) | ((sum >> 8) & 0xa8) | (((sum & ADDRMASK) == 0) << 6) |
					cbits2Z80Table[((HL ^ SP ^ sum) >> 8) & 0x1ff];
				HL = sum;
				break;

			case 0x73:      /* LD (nnnn),SP */
				temp = GET_WORD(PC);
				PUT_WORD(temp, SP);
				PC += 2;
				break;

			case 0x78:      /* IN A,(C) */
				temp = cpu_in(LOW_REGISTER(BC));
				SET_HIGH_REGISTER(AF, temp);
				AF = (AF & ~0xfe) | rotateShiftTable[temp & 0xff];
				break;

			case 0x79:      /* OUT (C),A */
				cpu_out(LOW_REGISTER(BC), HIGH_REGISTER(AF));
				break;

			case 0x7a:      /* ADC HL,SP */
				HL &= ADDRMASK;
				SP &= ADDRMASK;
				sum = HL + SP + TSTFLAG(C);
				AF = (AF & ~0xff) | ((sum >> 8) & 0xa8) | (((sum & ADDRMASK) == 0) << 6) |
					cbitsZ80Table[(HL ^ SP ^ sum) >> 8];
				HL = sum;
				break;

			case 0x7b:      /* LD SP,(nnnn) */
				temp = GET_WORD(PC);
				SP = GET_WORD(temp);
				PC += 2;
				break;

			case 0xa0:      /* LDI */
				acu = RAM_PP(HL);
				PUT_BYTE_PP(DE, acu);
				acu += HIGH_REGISTER(AF);
				AF = (AF & ~0x3e) | (acu & 8) | ((acu & 2) << 4) |
					(((--BC & ADDRMASK) != 0) << 2);
				break;

			case 0xa1:      /* CPI */
				acu = HIGH_REGISTER(AF);
				temp = RAM_PP(HL);
				sum = acu - temp;
				cbits = acu ^ temp ^ sum;
				AF = (AF & ~0xfe) | (sum & 0x80) | (!(sum & 0xff) << 6) |
					(((sum - ((cbits & 16) >> 4)) & 2) << 4) | (cbits & 16) |
					((sum - ((cbits >> 4) & 1)) & 8) |
					((--BC & ADDRMASK) != 0) << 2 | 2;
				if ((sum & 15) == 8 && (cbits & 16) != 0)
					AF &= ~8;
				break;
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
