mecparts/TeensyBoardZ80/src/cios.h

#define USE_CIOS
static const uint8 cios[] = {
	0x5A,0x53,0x44,0x4F,0x53,0x20,0xC3,0x9C,
	0x00,0x00,0x00,0x00,0x00,0x00,0x00,0x00,
	0x00,0x00,0x00,0x4B,0x00,0x4D,0x54,0x02,
	0x54,0x02,0x54,0x02,0x54,0x02,0x54,0x02,
	0x54,0x02,0x00,0x00,0x54,0x02,0x00,0x00,
	0x00,0x00,0x00,0x00,0x00,0x00,0x80,0x00,
	0x00,0x00,0x00,0x00,0x00,0x00,0x00,0x00,
	0x00,0x00,0x00,0x00,0x00,0x00,0x00,0x00,
	0x00,0x00,0x00,0x00,0x00,0x00,0x00,0x00,
	0x00,0x00,0x00,0x00,0x00,0x00,0x00,0x00,
	0x00,0x00,0x00,0x00,0x00,0x00,0x00,0x00,
	0x00,0x00,0x00,0x00,0x00,0x00,0x00,0x00,
	0x00,0x00,0x00,0x00,0x00,0x00,0x00,0x00,
	0x00,0x00,0x00,0x00,0x00,0x00,0x00,0x00,
	0x00,0x00,0x00,0x00,0x00,0x00,0x00,0x00,
	0x00,0x00,0x00,0x00,0x00,0x00,0x00,0x00,
	0x00,0x00,0x00,0x00,0x00,0x00,0x00,0x00,
	0x00,0x00,0x00,0x00,0x00,0x00,0x00,0x00,
	0x00,0x00,0x00,0x00,0x00,0x00,0x00,0x00,
	0x00,0x00,0x00,0x00,0x79,0x32,0x4B,0x00,
	0x21,0x00,0x00,0x22,0x4C,0x00,0xED,0x73,
	0x62,0x00,0x31,0x9C,0x00,0xDD,0xE5,0xD5,
	0xDD,0xE1,0xDD,0x22,0x5F,0x00,0x21,0x55,
	0x02,0xE5,0x79,0xFE,0x0C,0x38,0x11,0xD1,
	0xDD,0xE5,0xD1,0xDD,0xE1,0x3A,0x4B,0x00,
	0x4F,0xED,0x7B,0x62,0x00,0xDB,0x00,0xC9,
	0x21,0xDE,0x00,0x06,0x00,0x09,0x09,0x7E,
	0x23,0x66,0x6F,0x4B,0x7B,0xE9,0x03,0xF2,
	0x4B,0x01,0x58,0x01,0xBF,0x00,0xBF,0x00,
	0xBF,0x00,0x81,0x01,0xBF,0x00,0xBF,0x00,
	0xA0,0x01,0xAC,0x01,0x46,0x01,0xCD,0x0A,
	0x01,0x30,0x5D,0xF5,0x3E,0x5E,0xCD,0x58,
	0x01,0xF1,0xF5,0xC6,0x40,0xCD,0x58,0x01,
	0xF1,0xC9,0xFE,0x0D,0xC8,0xFE,0x0A,0xC8,
	0xFE,0x09,0xC8,0xFE,0x08,0xC8,0xFE,0x7F,
	0xC8,0xFE,0x20,0xC9,0x7E,0xDD,0x35,0x01,
	0x2B,0xDD,0xE5,0xE5,0x06,0x01,0xFE,0x09,
	0x28,0x05,0xFE,0x20,0x30,0x01,0x04,0xC5,
	0x0E,0x08,0xCD,0x0C,0xF2,0x0E,0x20,0xCD,
	0x0C,0xF2,0x0E,0x08,0xCD,0x0C,0xF2,0xC1,
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
};

static const uint8 cios_prl[] = {
	0x00,0x01,0x80,0xAA,0x22,0x00,0x00,0x00,
	0x00,0x00,0x00,0x00,0x00,0x00,0x00,0x00,
	0x00,0x00,0x00,0x80,0x20,0x12,0x20,0x01,
	0x80,0x10,0x04,0x00,0xAA,0xAA,0x2A,0x01,
	0x81,0x00,0x00,0x00,0x00,0x00,0x00,0x00,
	0x00,0x00,0x40,0x00,0x00,0x00,0x01,0x20,
	0x00,0x00,0x00,0x00,0x00,0x01,0x00,0x00,
	0x00,0x00,0x00,0x00,0x80,0x00,0x00,0x10,
	0x40,0x00,0x42,0x80,0x00,0x04,0x10,0x02,
	0x00,0x08,0x08,0x11,0x49,0x00,0x00,0x00
};
//
